lucaskirschner/trabajo-final-cese/memoria/Figures/integracion_entradas.pdf

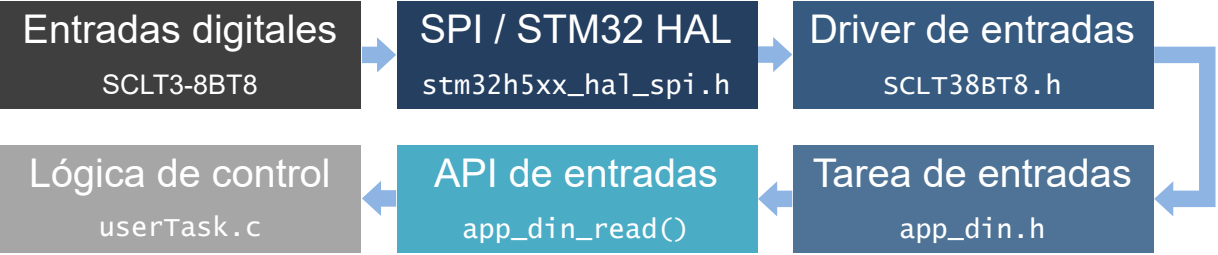
[picture p3: figure]
Entradas digitales; SCLT3-8BT8; SPI / STM32 HAL; stm32h5xx_hal_spi.h; Driver de entradas; SCLT38BT8.h; Tarea de entradas; app_din.h; API de entradas; app_din_read(); Lógica de control; userTask.c
