lucaskirschner/trabajo-final-cese/memoria/Figures/integracion_rf.pdf

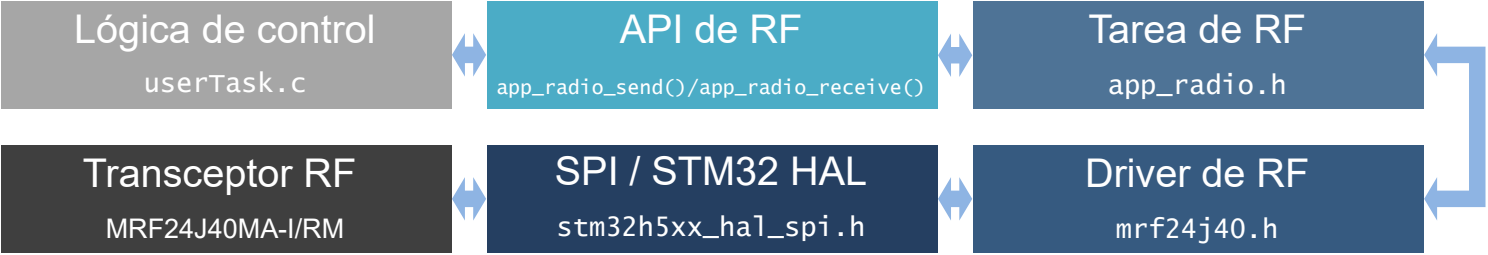
[picture p4: figure]
Transceptor RF; MRF24J40MA-I/RM; SPI / STM32 HAL; stm32h5xx_hal_spi.h; Driver de RF; mrf24j40.h; Lógica de control; userTask.c; API de RF; app_radio_send()/app_radio_receive(); Tarea de RF; app_radio.h
