lucaskirschner/trabajo-final-cese/memoria/Figures/integracion_rs485.pdf

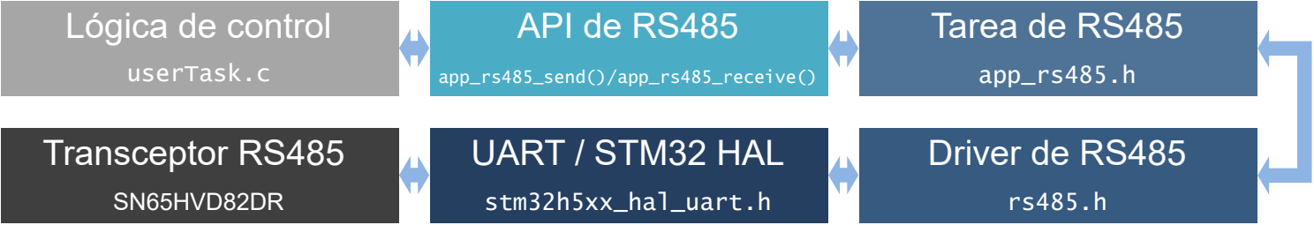
[picture p5: figure]
Transceptor RS485; SN65HVD82DR; UART / STM32 HAL; stm32h5xx_hal_uart.h; Driver de RS485; Lógica de control; userTask.c; API de RS485; app_rs485_send()/app_rs485_receive(); Tarea de RS485; app_rs485.h
