lucaskirschner/trabajo-final-cese/memoria/Figures/integracion_salidas.pdf

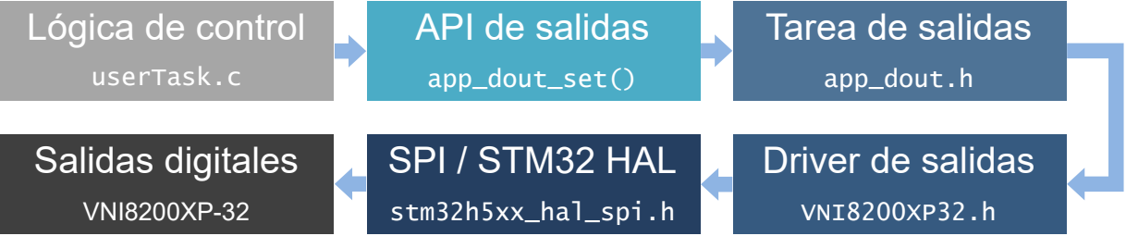
[picture p6: figure]
Salidas digitales; VNI8200XP-32; SPI / STM32 HAL; stm32h5xx_hal_spi.h; Driver de salidas; VNI8200XP32.h; Lógica de control; userTask.c; API de salidas; app_dout_set(); Tarea de salidas; app_dout.h
