lucaskirschner/trabajo-final-cese/memoria/Figures/red_control_distribuida.pdf

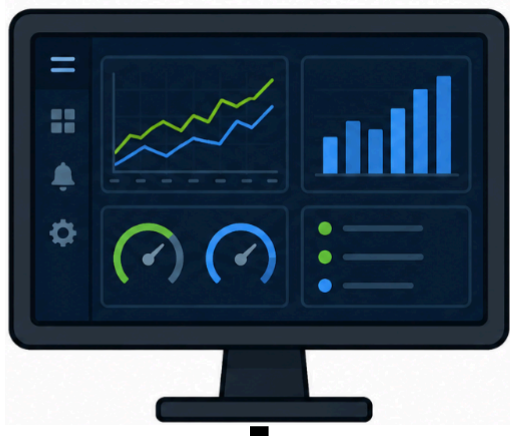
[picture p8: figure]

## SUPERVISIÓN

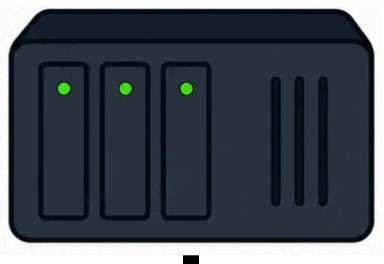
[picture p9: figure]

## CONTROL

## CAMPO

INTERFAZ DE
SUPERVISIÓN

ESTACIÓN
CENTRAL

ESTACIÓN
REMOTA 1

ESTACIÓN
REMOTA 2

SENSOR DE

PROXIMIDAD | CONTACTOR | SENSOR DE
CAUDAL | ELECTROVÁLVULA
