lucaskirschner/trabajo-final-cese/memoria/Releases/TI_Kirschner_Lucas_V4_vs_V5.pdf

# Draftable Comparison Export

This document is an exported comparison with limited functionality, generated by Draftable Desktop. To access full functionality, use Draftable's powerful comparison viewer in any of our products.
Left document: | TI_Kirschner_Lucas_V4.pdf
Right document: | TI_Kirschner_Lucas_V5.pdf

## What is this document?

This is a comparison of two documents. The two documents are interleaved such that the left document is displayed on even pages and the right document is displayed on odd pages.

## Is there a specific way I should view this file?

This document is intended to be viewed in Two Page Continuous mode (or sometimes called 'Two Page Scrolling'). It should open in this mode by default when using Adobe Acrobat and most popular PDF readers.

If the document opens in a different view, you can often change this in the settings. In Adobe Acrobat, go to View > Page Display > Two Page Scrolling.

## Why are there blank pages?

Blank pages are inserted to keep both documents as aligned as much as possible.
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
