lucaskirschner/trabajo-final-cese/hardware/dev/Rev/MEC-V1.0-Sch RevA.pdf

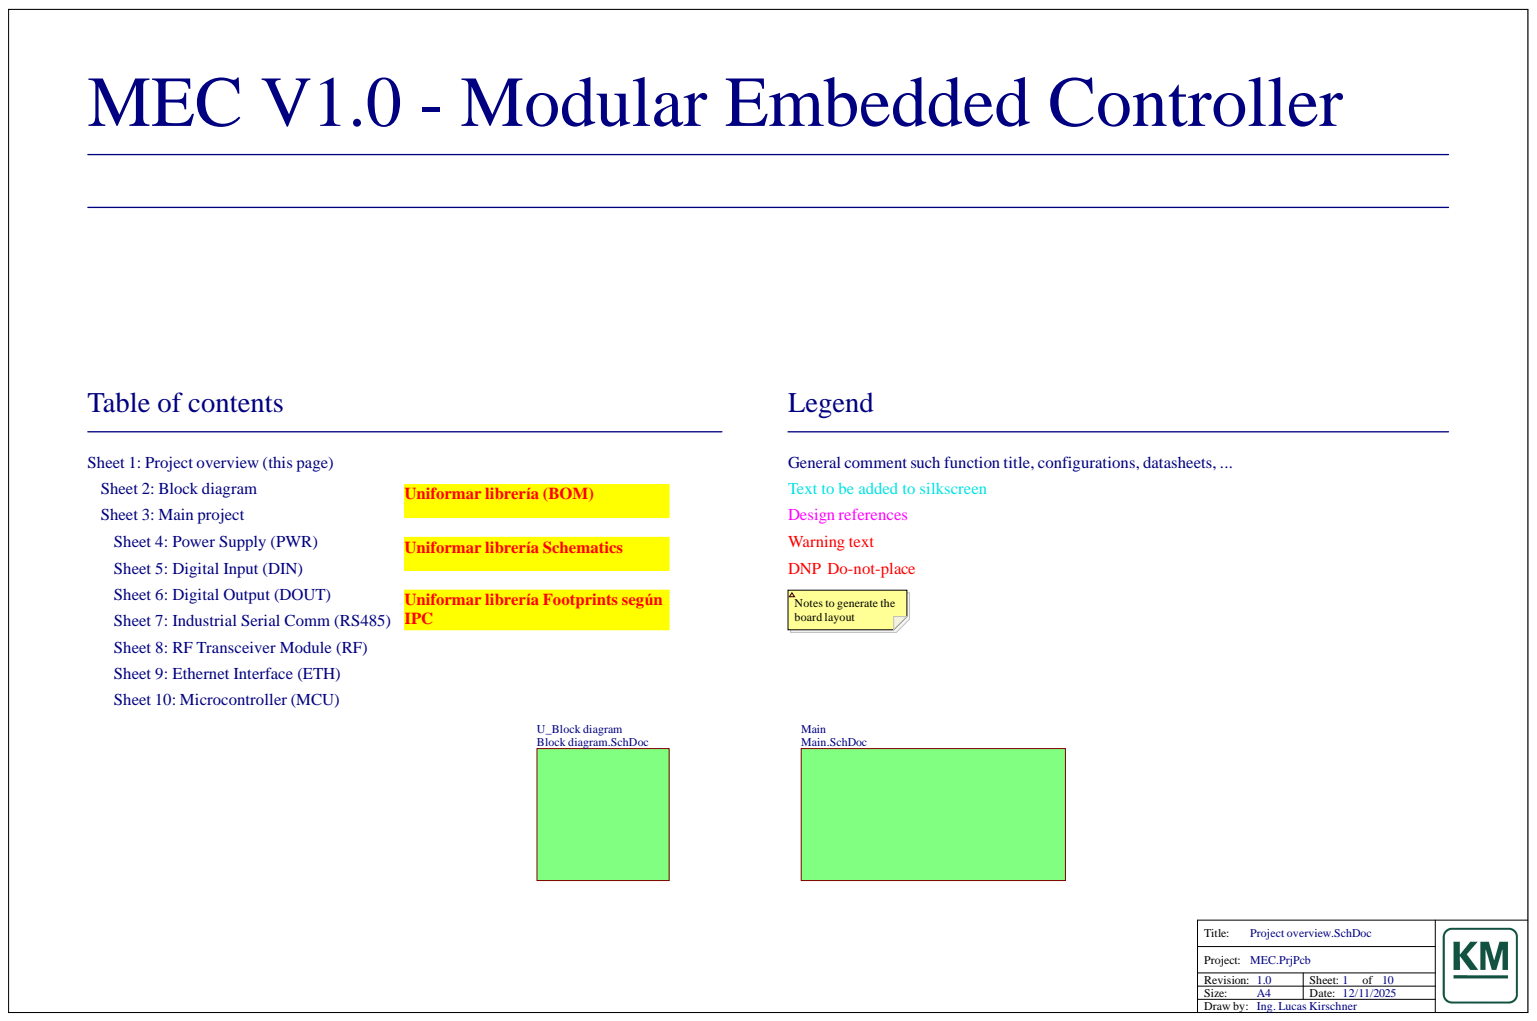
[picture p63: page 1]

MEC V1.0 - Modular Embedded Controller

Sheet 1: Project overview (this page)
Sheet 2: Block diagram
Sheet 3: Main project
Sheet 4: Power Supply (PWR)
Sheet 5: Digital Input (DIN)
Sheet 6: Digital Output (DOUT)
Sheet 7: Industrial Serial Comm (RS485)
Sheet 8: RF Transceiver Module (RF)
Sheet 9: Ethernet Interface (ETH)
Sheet 10: Microcontroller (MCU)

General commentsuch function title, configurations, datasheets, ...
Text to be added to silkscreen
Design references
Warning text
DNP Do-not-place

Uniformar librería Footprints según
IPC

Notes to generate the
board layout

Revision: 1.0 | Sheet: 1 of 10
Size: A4 | Date:


Reservado diagrama de bloques

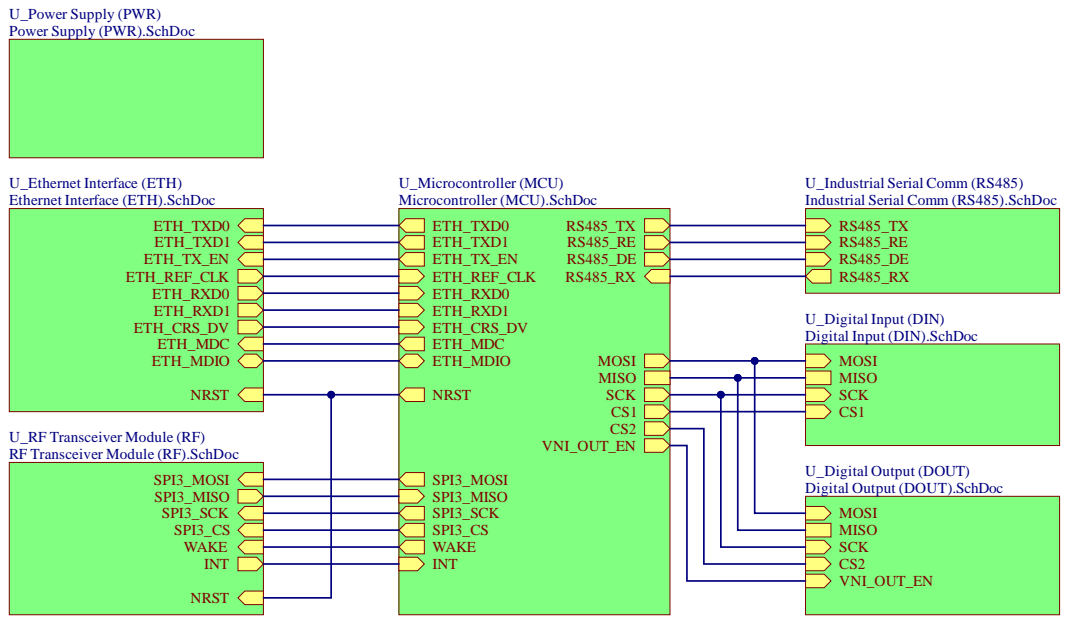
[picture p64: page 3]

U_Power Supply (PWR)
Power Supply (PWR).SchDoc

U_Ethernet Interface (ETH)
Ethernet Interface (ETH).SchDoc

U_RF Transceiver Module (RF)
RF Transceiver Module (RF).SchDoc

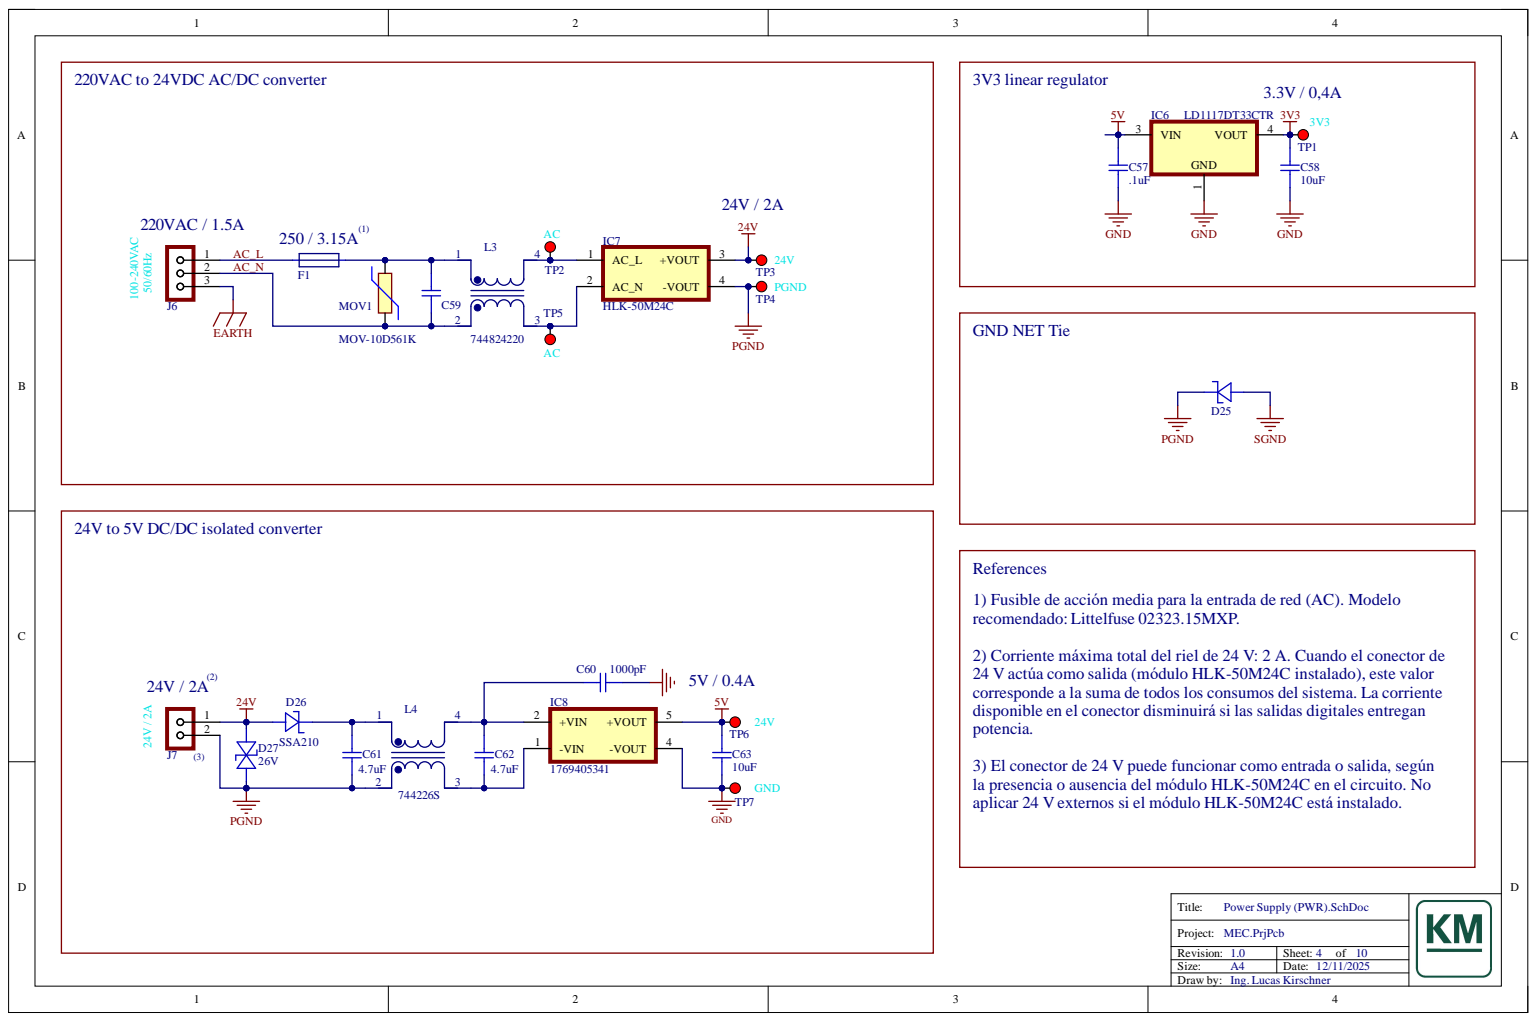
[picture p65: page 4]

220VAC to 24VDC AC/DC converter

24V to 5V DC/DC isolated converter

1) Fusible de acción media para la entrada de red (AC). Modelo
recomendado: Littelfuse 02323.15MXP.

2) Corriente máxima total del riel de 24 V: 2 A. Cuando el conector de
24 V actúa como salida (módulo HLK-50M24C instalado), este valor
corresponde a la suma de todos los consumos del sistema. La corriente
disponible en el conector disminuirá si las salidas digitales entregan
potencia.

3) El conector de 24 V puede funcionar como entrada o salida, según
la presencia o ausencia del módulo HLK-50M24C en el circuito. No
aplicar 24 V externos si el módulo HLK-50M24C está instalado.

Power Supply (PWR).SchDoc

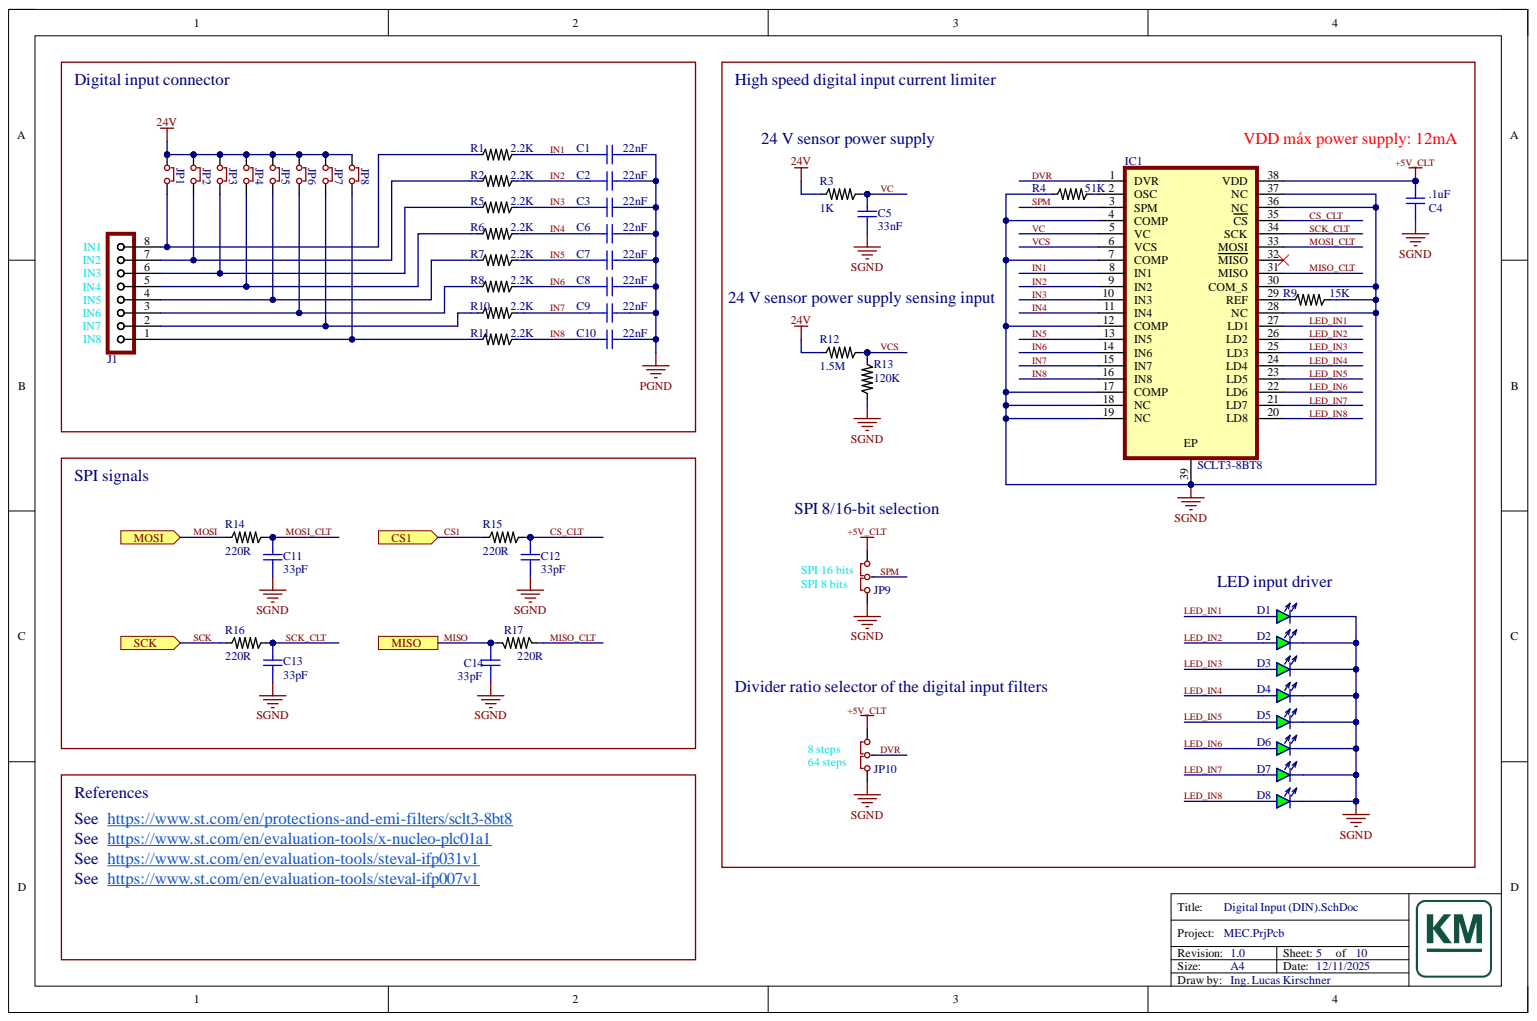
[picture p66: page 5]

3 5 3 4 3 3 3 2 | C S_C LT S CK_C LT MOS I_C LT M I SO_C LT

V sensor power supply sensing

Rev i s i o n : 1 . 0 | Sheet : o f 1 0
Size : A | Dat e : / /

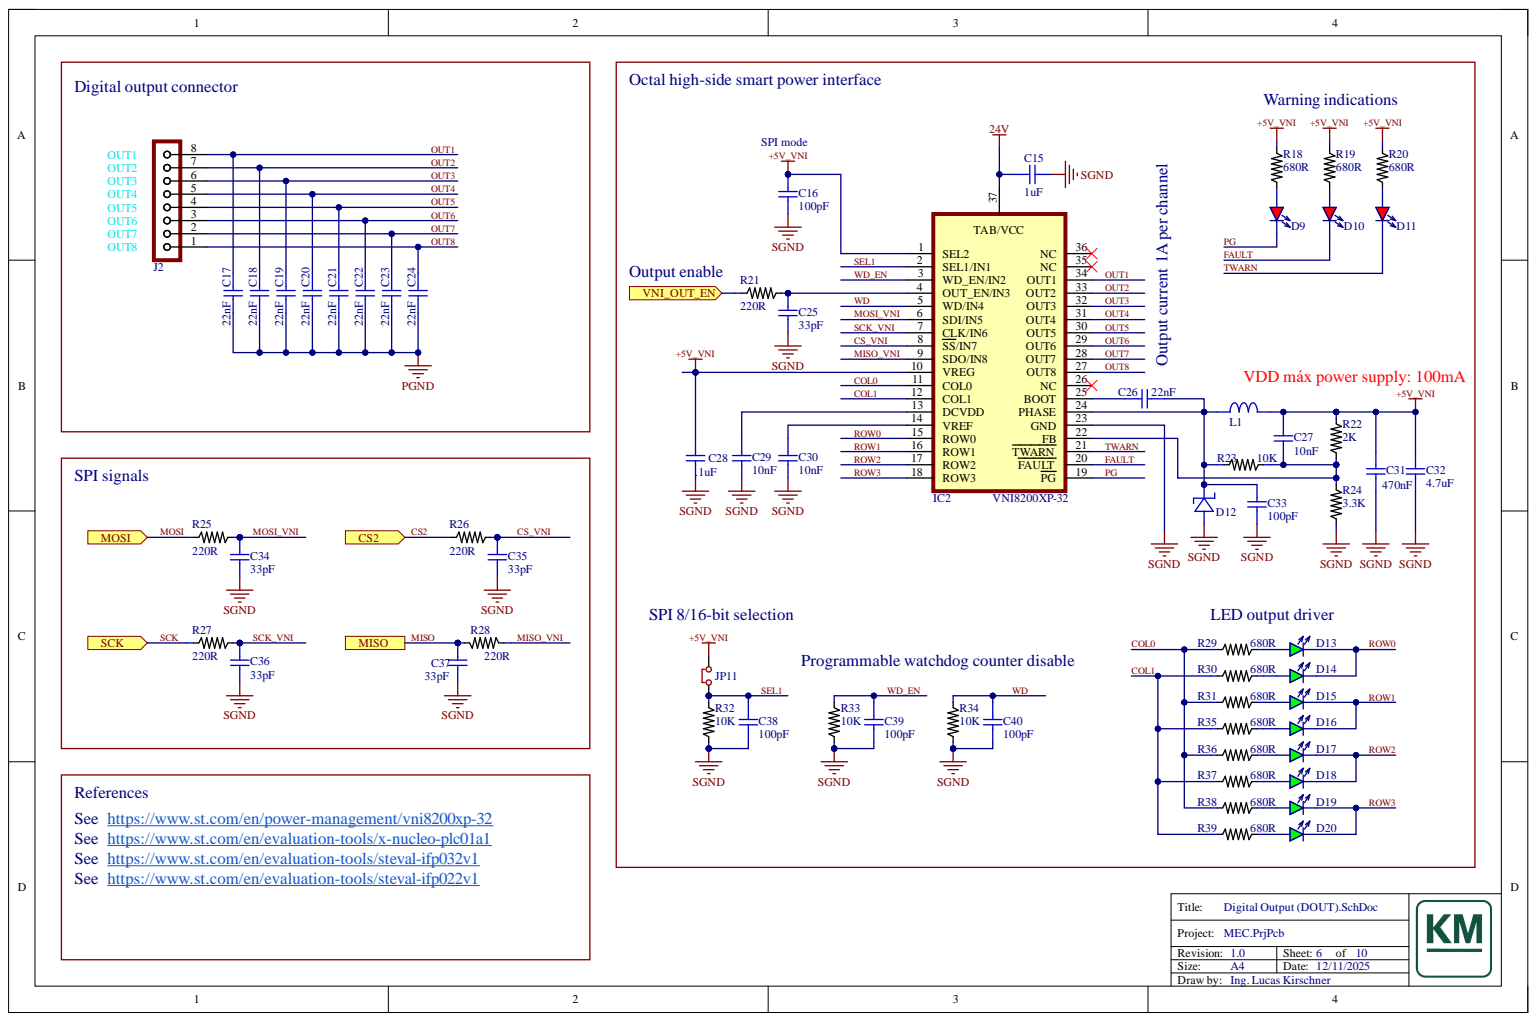
[picture p67: page 6]

Warning indications +5V_VNI +5V_VNI +5V_VNI

Output current 1A per channel

VDD máx power supply: 100mA

Programmable watchdog counter disable

References
See https://www.st.com/en/power-management/vni8200xp-32
See https://www.st.com/en/evaluation-tools/x-nucleo-plc01a1
See https://www.st.com/en/evaluation-tools/steval-ifp032v1
See https://www.st.com/en/evaluation-tools/steval-ifp022v1

Digital Output (DOUT).SchDoc

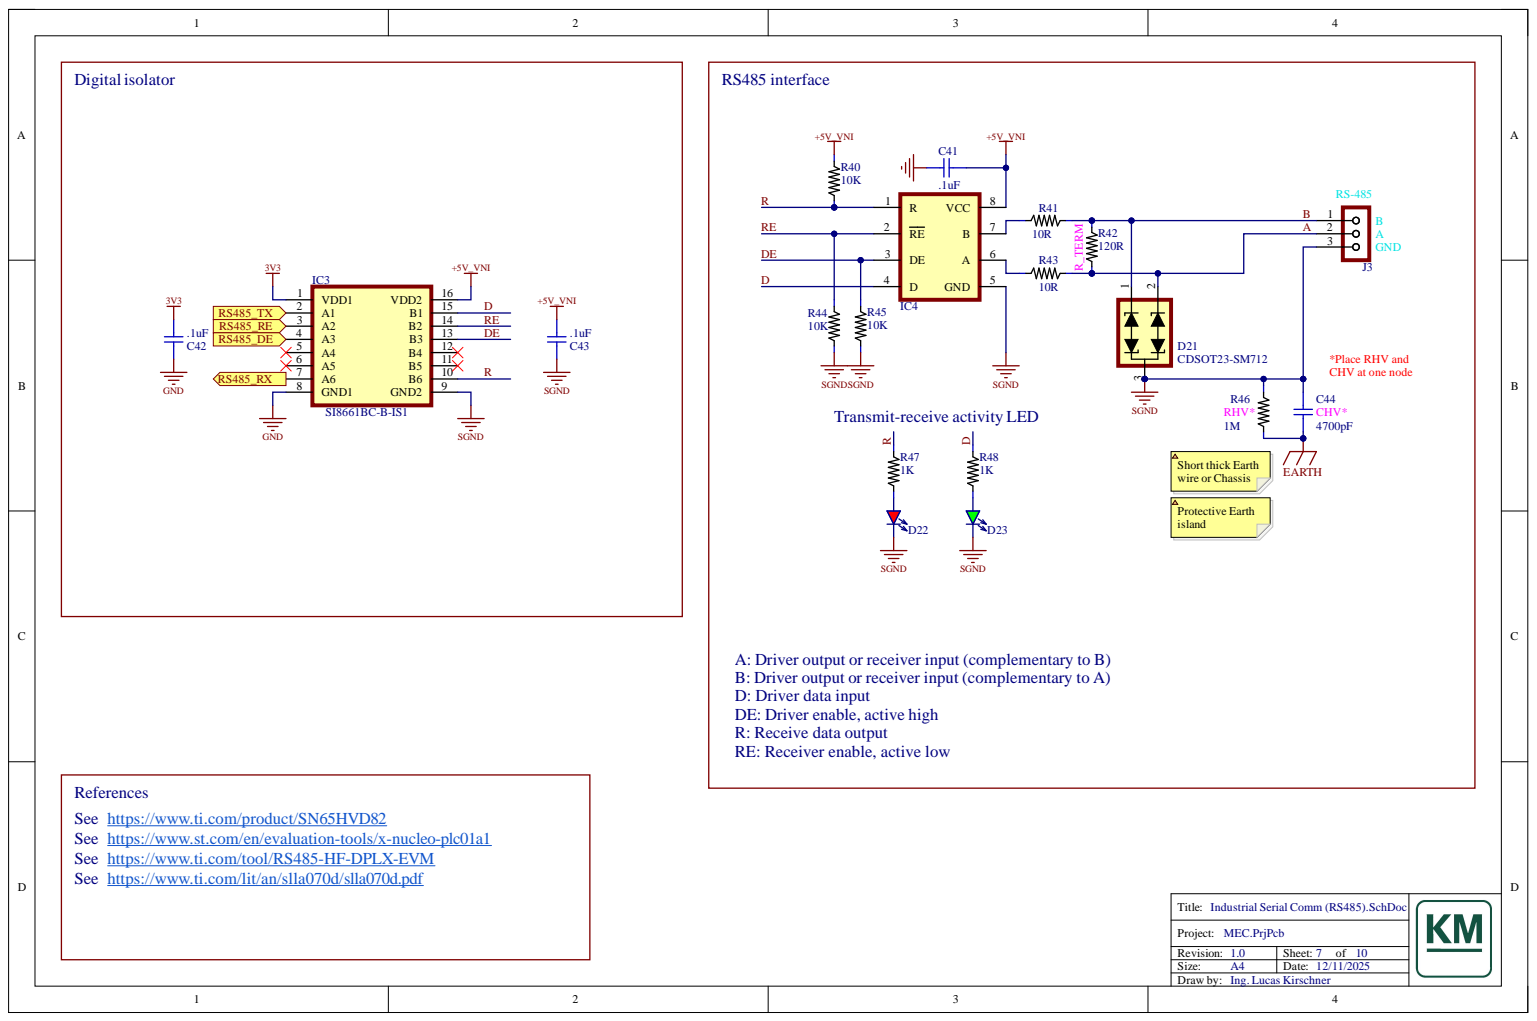
[picture p68: page 7]

Driver output or receiver

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

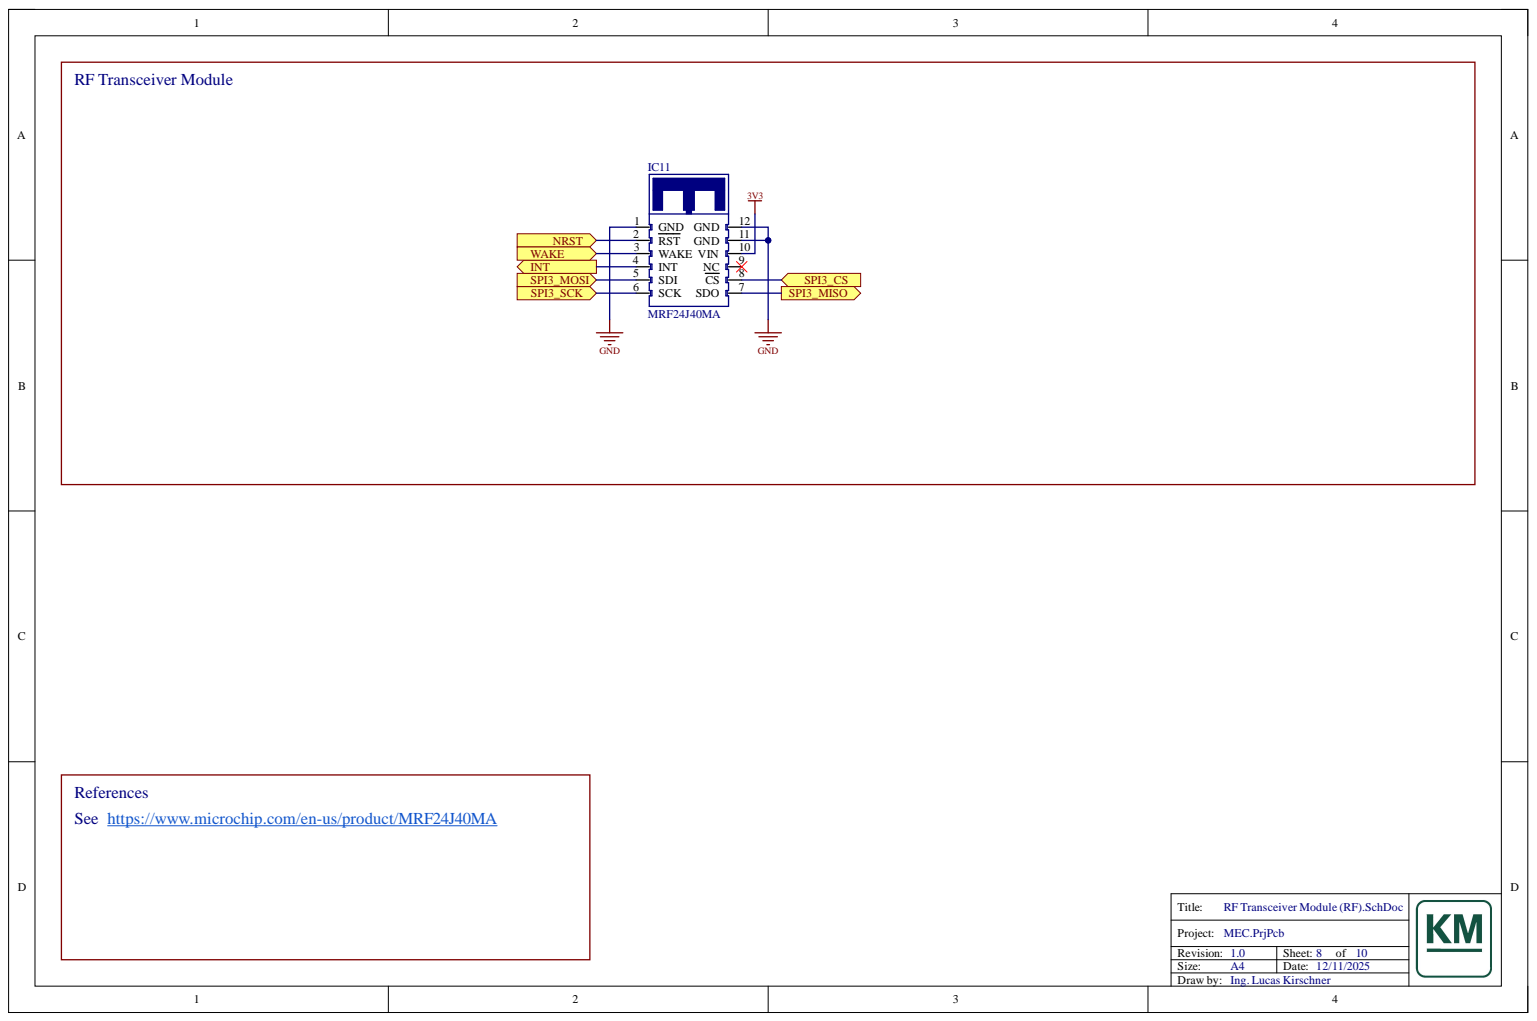
[picture p69: page 8]

References
See https://www.microchip.com/en-us/product/MRF24J40MA

RF Transceiver Module (RF).SchDoc

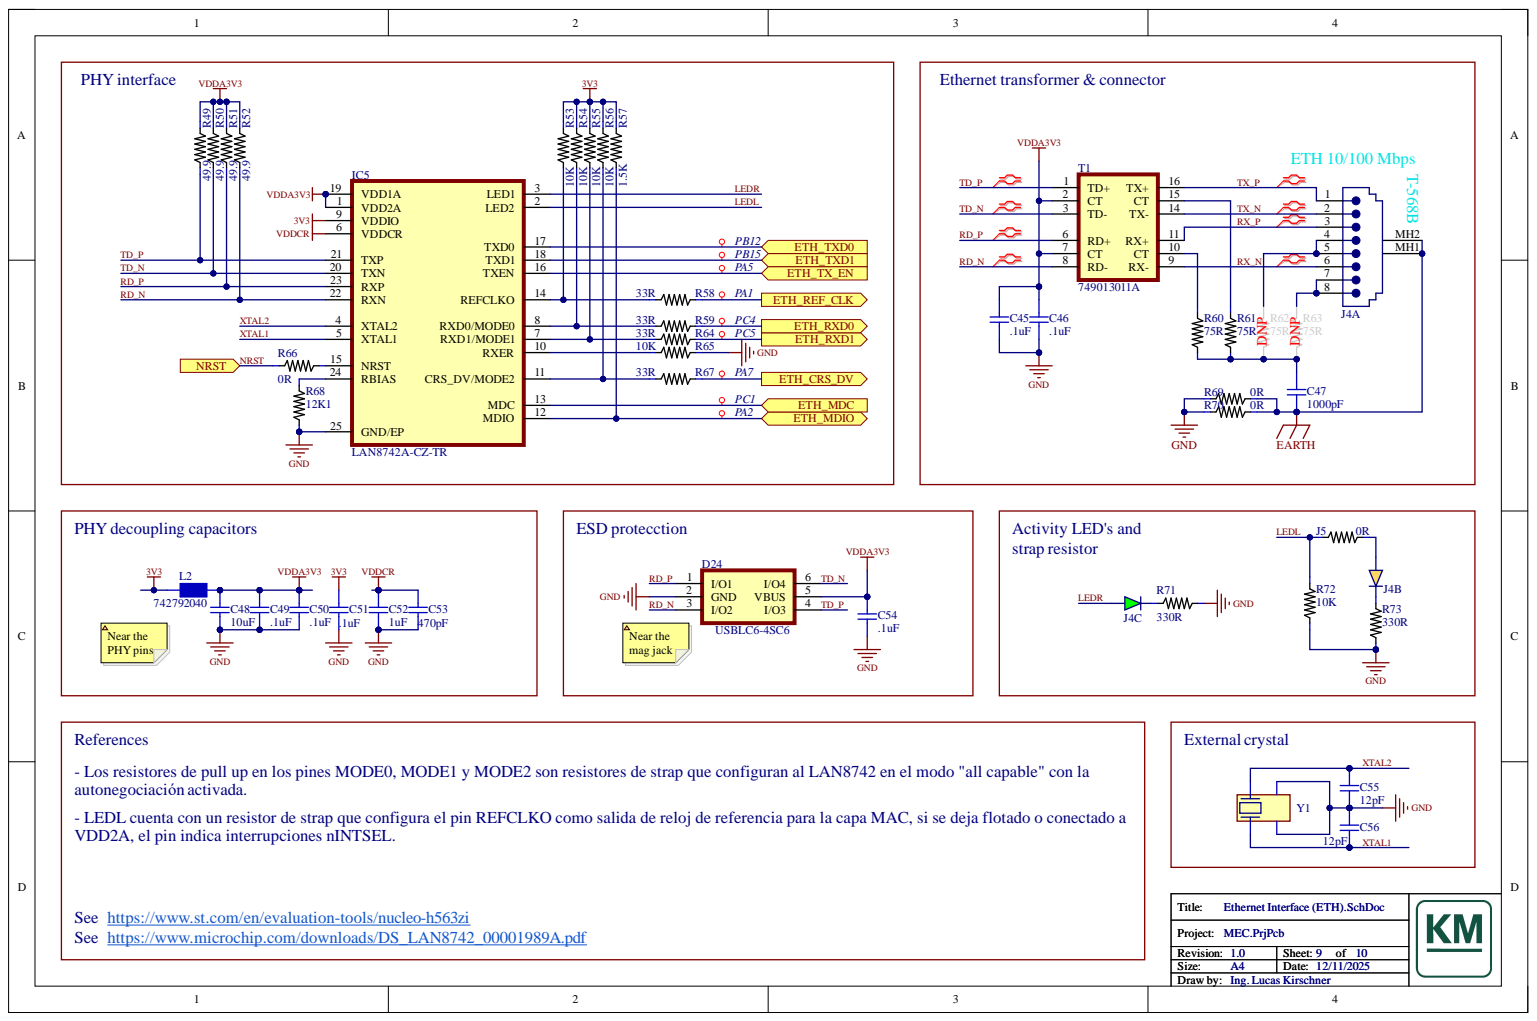
[picture p70: page 9]

- Los resistores de pull up en los pines MODE0, MODE1 y MODE2 son resistores de strap que configuran al LAN8742 en el modo "all capable" con la
autonegociación activada.
- LEDL cuenta con un resistor de strap que configura el pin REFCLKO como salida de reloj de referencia para la capa MAC, si se deja flotado o conectado a
VDD2A, el pin indica interrupciones nINTSEL.

See https://www.st.com/en/evaluation-tools/nucleo-h563zi
See https://www.microchip.com/downloads/DS_LAN8742_00001989A.pdf (https://ww1.microchip.com/downloads/aemDocuments/documents/OTH/ProductDocuments/DataSheets/DS_LAN8742_00001989A.pdf)

Ethernet Interface (ETH).SchDoc

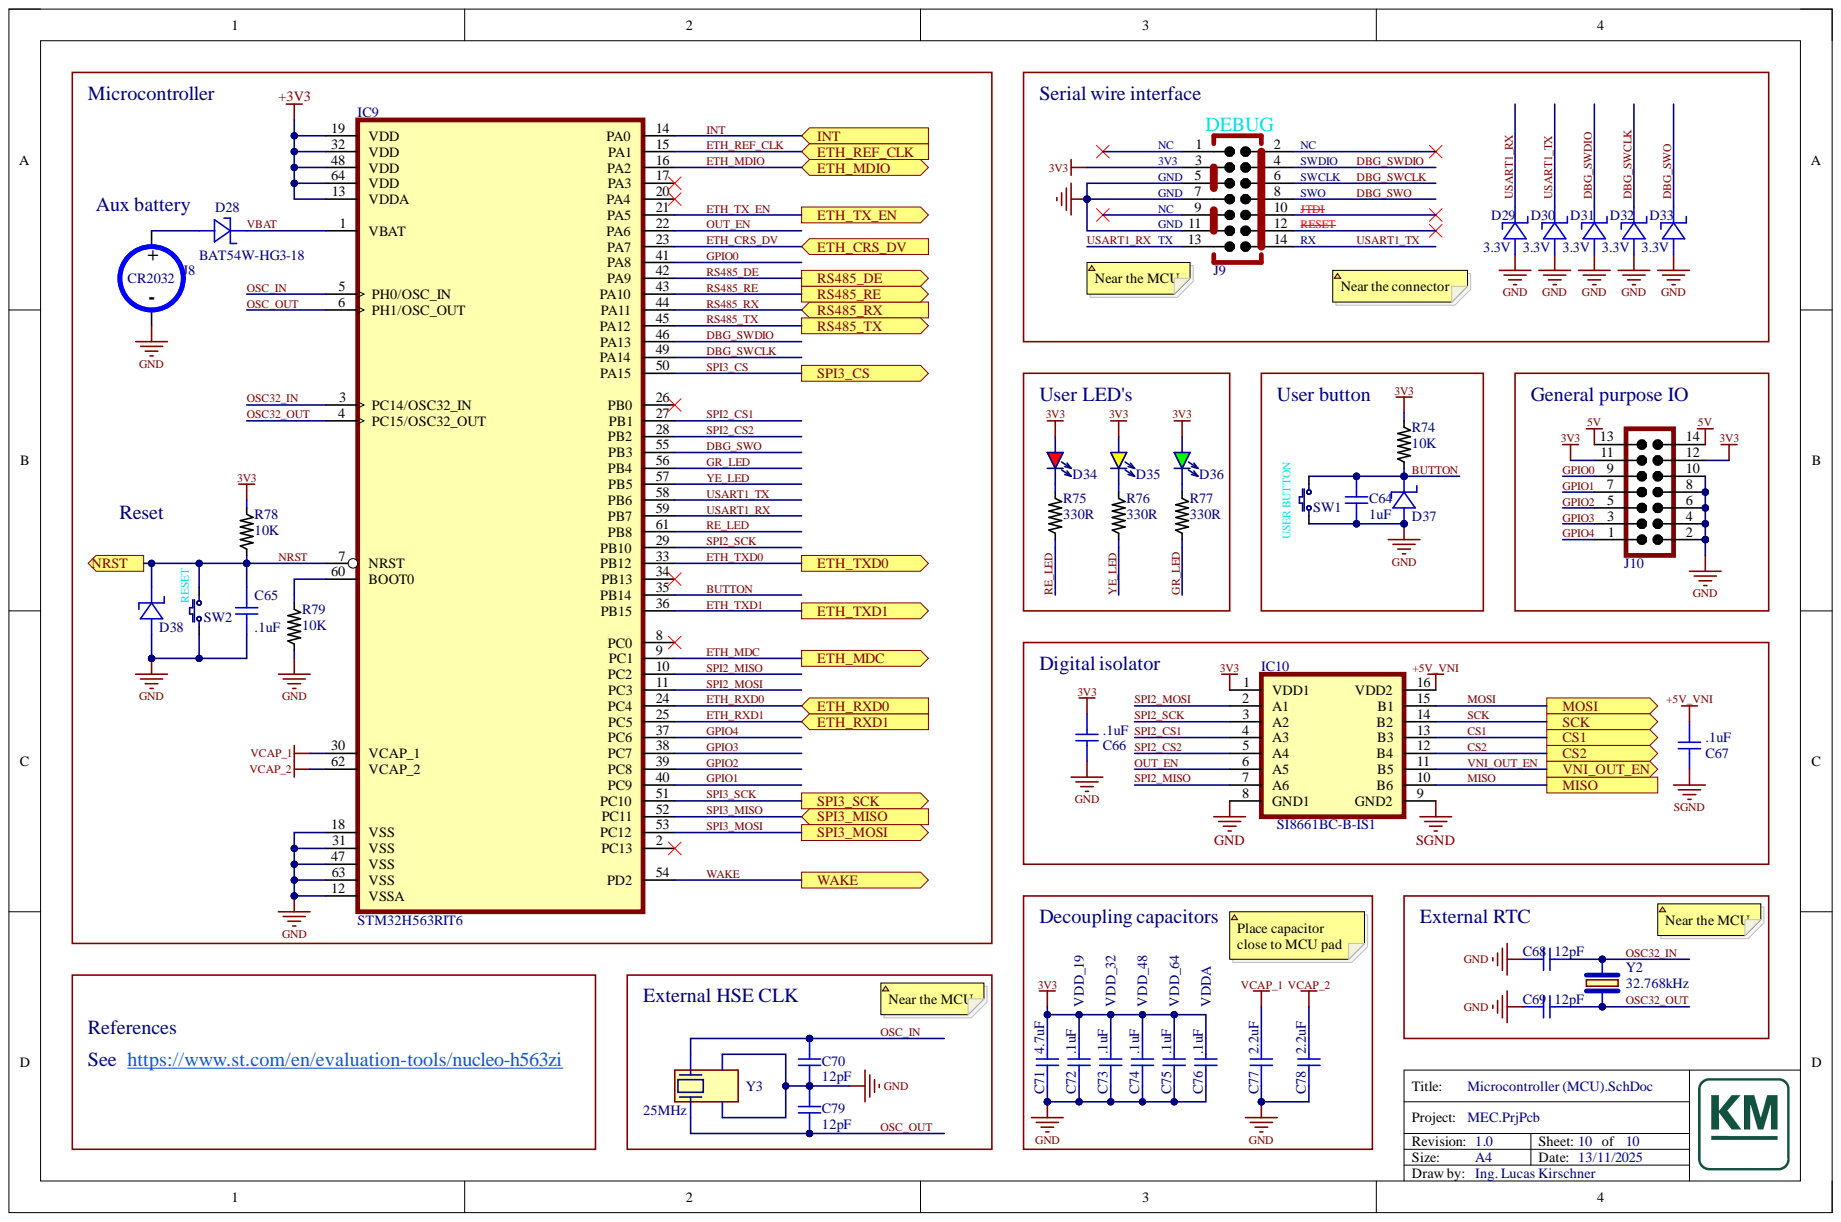
[picture p71: page 10]
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
