lucaskirschner/trabajo-final-cese/hardware/dev/Rev/MEC-V1.0-Sch RevB.pdf

MEC V1.0 - Modular Embedded Controller

Sheet 1: Project overview (this page)
Sheet 2: Block diagram
Sheet 3: Main project
Sheet 4: Power Supply (PWR)
Sheet 5: Digital Input (DIN)
Sheet 6: Digital Output (DOUT)
Sheet 7: Industrial Serial Comm (RS485)
Sheet 8: RF Transceiver Module (RF)
Sheet 9: Ethernet Interface (ETH)
Sheet 10: Microcontroller (MCU)

General commentsuch function title, configurations, datasheets, ...
Text to be added to silkscreen
Design references
Warning text
DNP Do-not-place

Uniformar librería Footprints según
IPC

Notes to generate the
board layout

Revision: 1.0 | Sheet: 1 of 10
Size: A4 | Date:


Reservado diagrama de bloques


U_Power Supply (PWR)
Power Supply (PWR).SchDoc

U_Ethernet Interface (ETH)
Ethernet Interface (ETH).SchDoc

U_RF Transceiver Module (RF)
RF Transceiver Module (RF).SchDoc

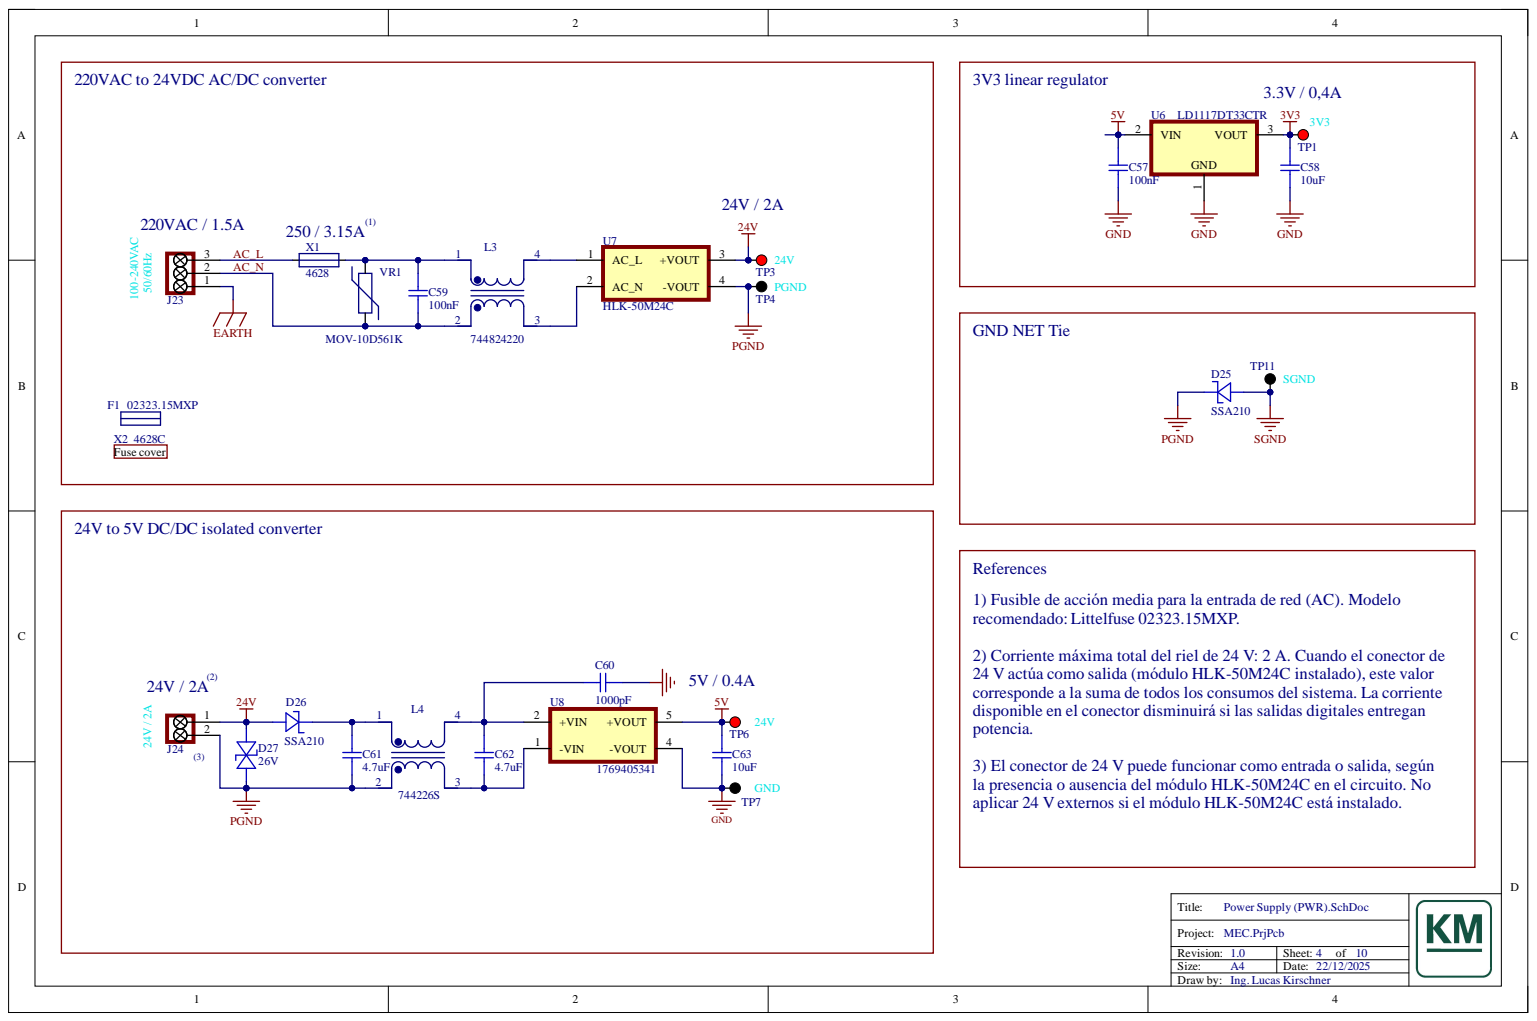
[picture p72: page 4]

220VAC to 24VDC AC/DC converter

24V to 5V DC/DC isolated converter

1) Fusible de acción media para la entrada de red (AC). Modelo
recomendado: Littelfuse 02323.15MXP.

2) Corriente máxima total del riel de 24 V: 2 A. Cuando el conector de
24 V actúa como salida (módulo HLK-50M24C instalado), este valor
corresponde a la suma de todos los consumos del sistema. La corriente
disponible en el conector disminuirá si las salidas digitales entregan
potencia.

3) El conector de 24 V puede funcionar como entrada o salida, según
la presencia o ausencia del módulo HLK-50M24C en el circuito. No
aplicar 24 V externos si el módulo HLK-50M24C está instalado.

Power Supply (PWR).SchDoc

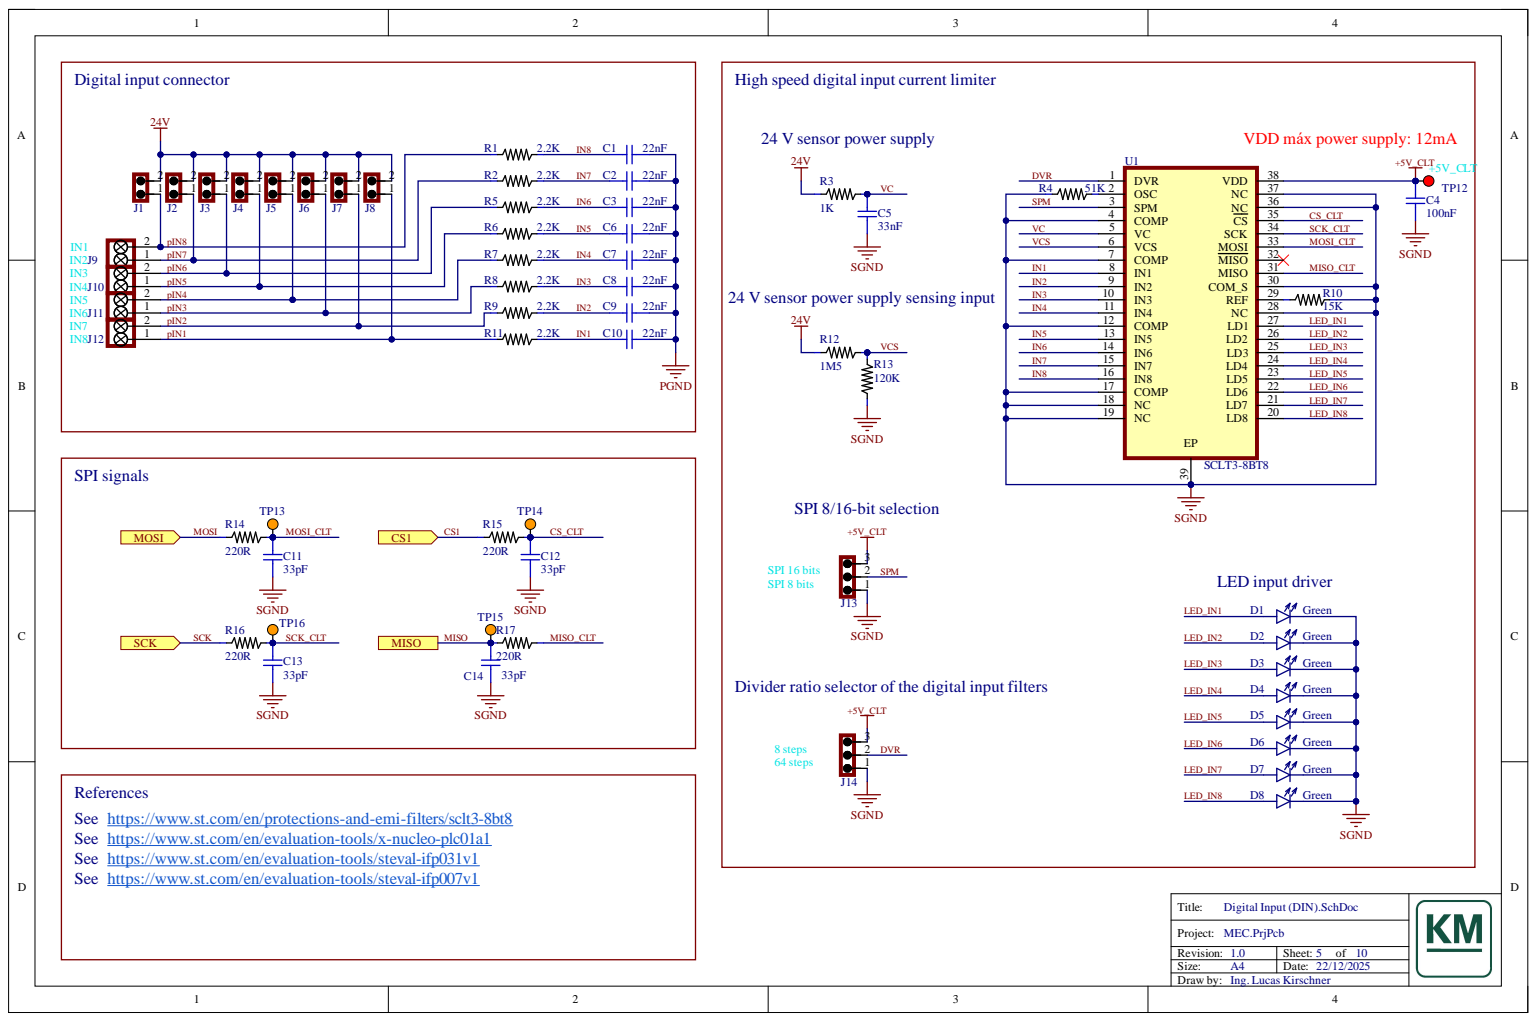
[picture p73: page 5]

pIN7 | R7

V sensor power supply sensing

Rev i s i o n : 1 . 0 | Sheet : o f 1 0
Size : A | Dat e /

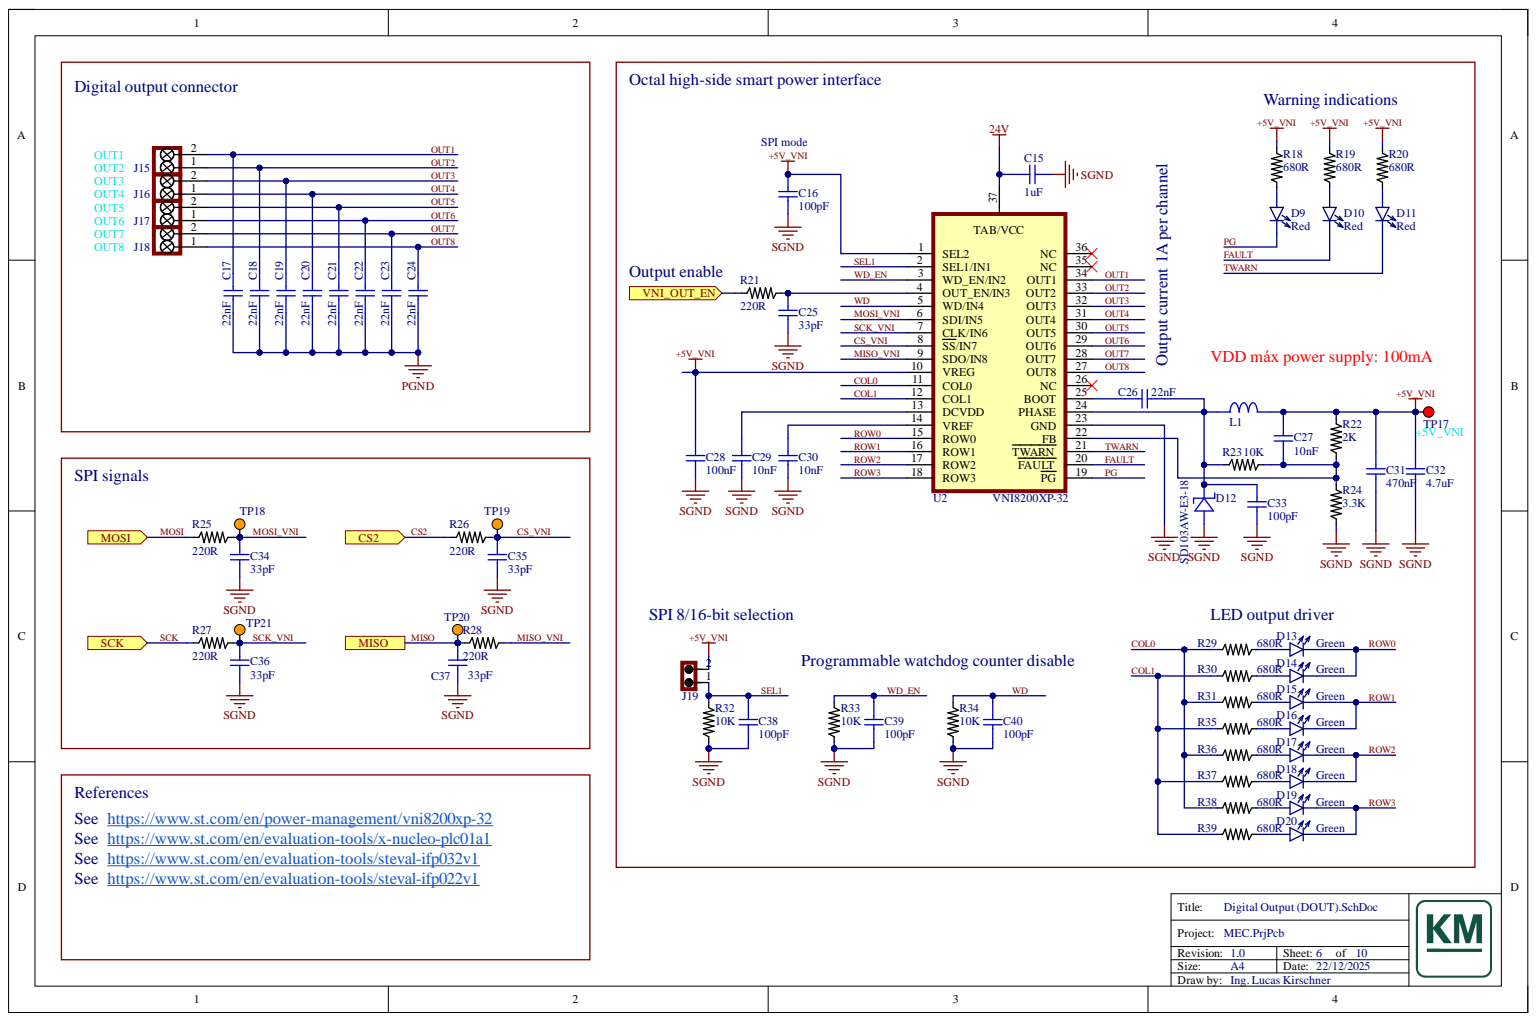
[picture p74: page 6]

Octal high-side smart power

Output current 1A per channel

12 | OUT 3

OUT 4

12 | | | OUT 5

OUT 6

12 | | | | | OUT 7

ion | | 2 1 | FAULT TWARN

SPI signal s SG SG | TP1 8 TP1 C3 4 N D SG TP2 0 TP2 1 C3 6 N D N D | 9 C3 5 N D

/en/power-management/vni
/en/evaluat
.com

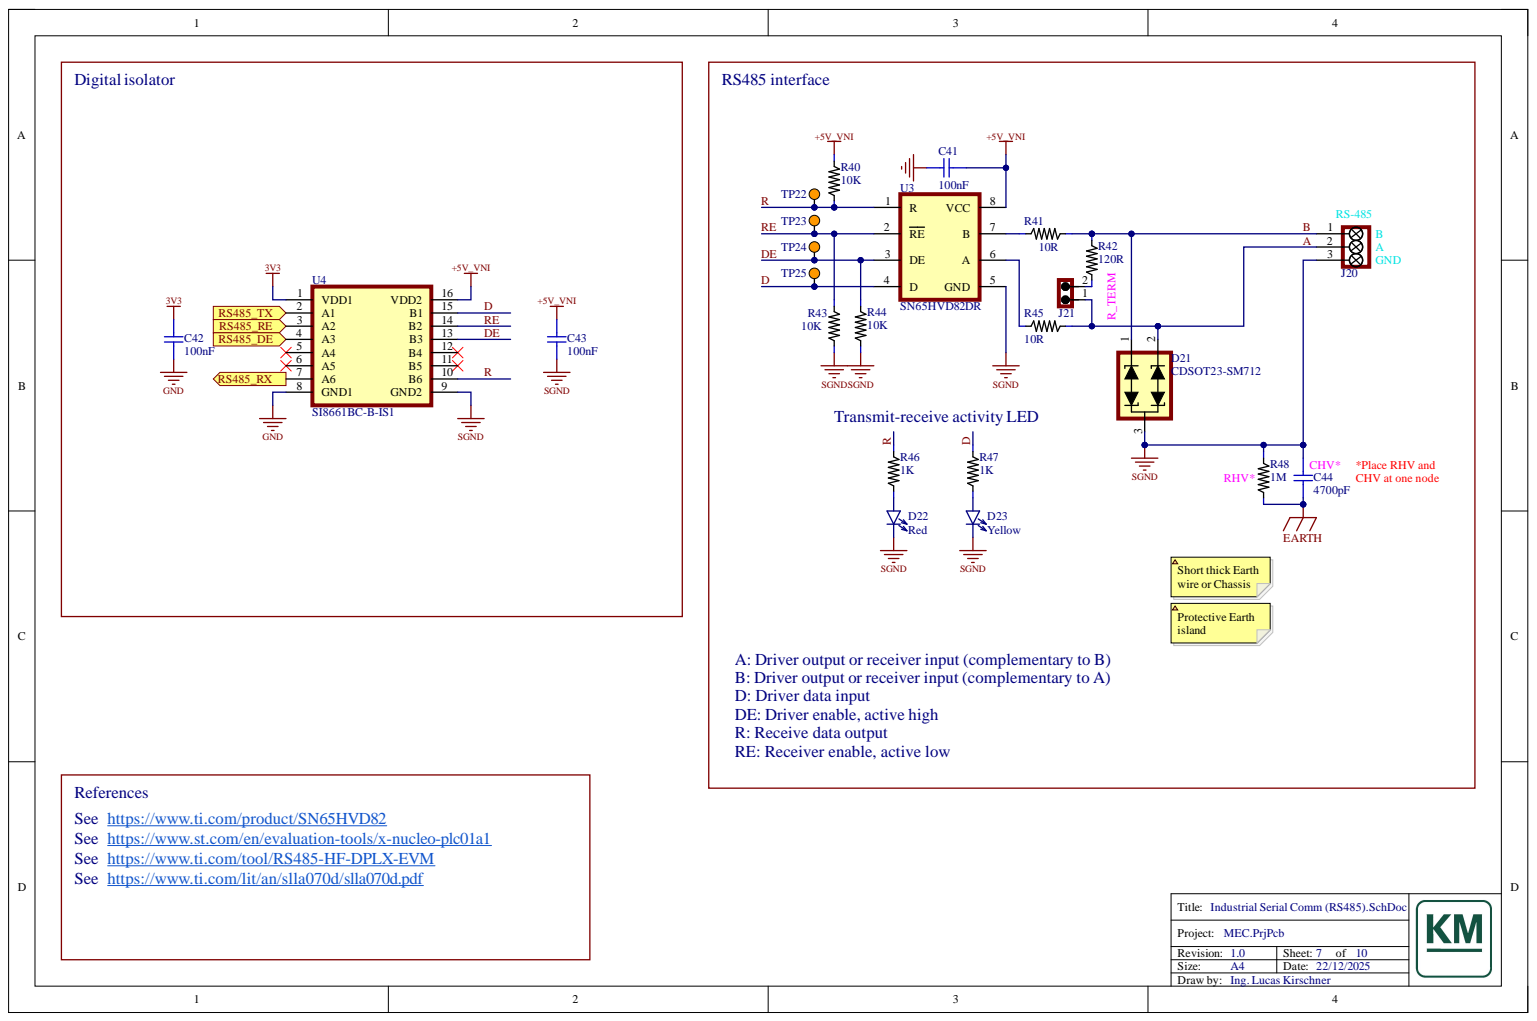
[picture p75: page 7]

Driver output or receiver

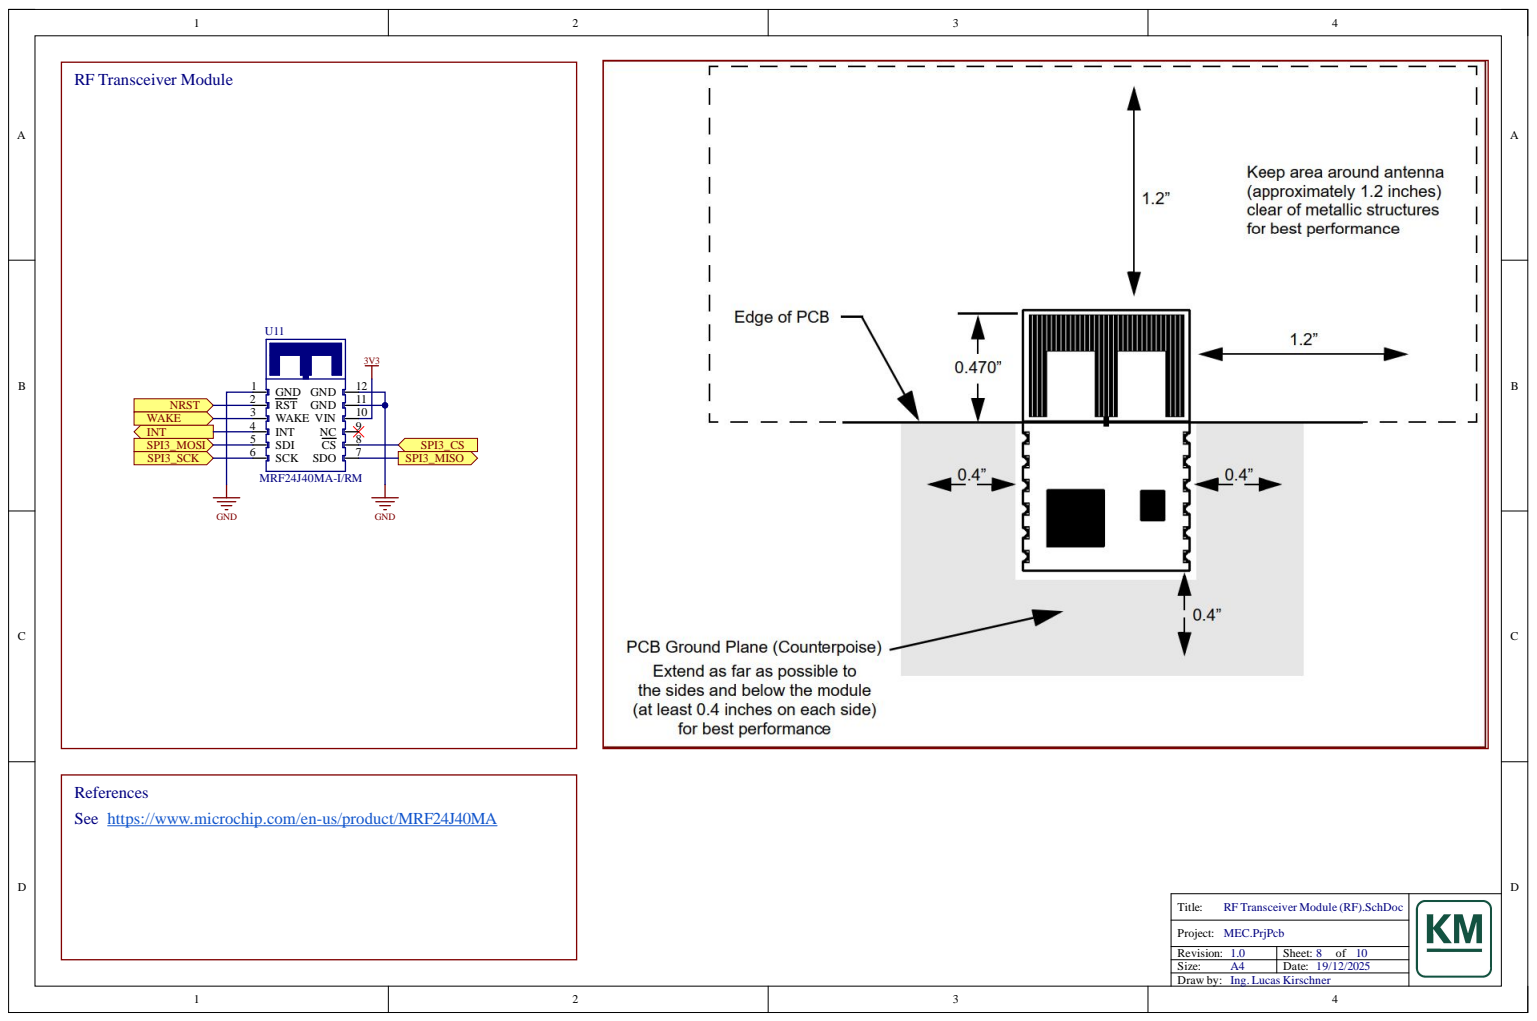
[picture p76: page 8]

References
See https://www.microchip.com/en-us/product/MRF24J40MA

RF Transceiver Module (RF).SchDoc

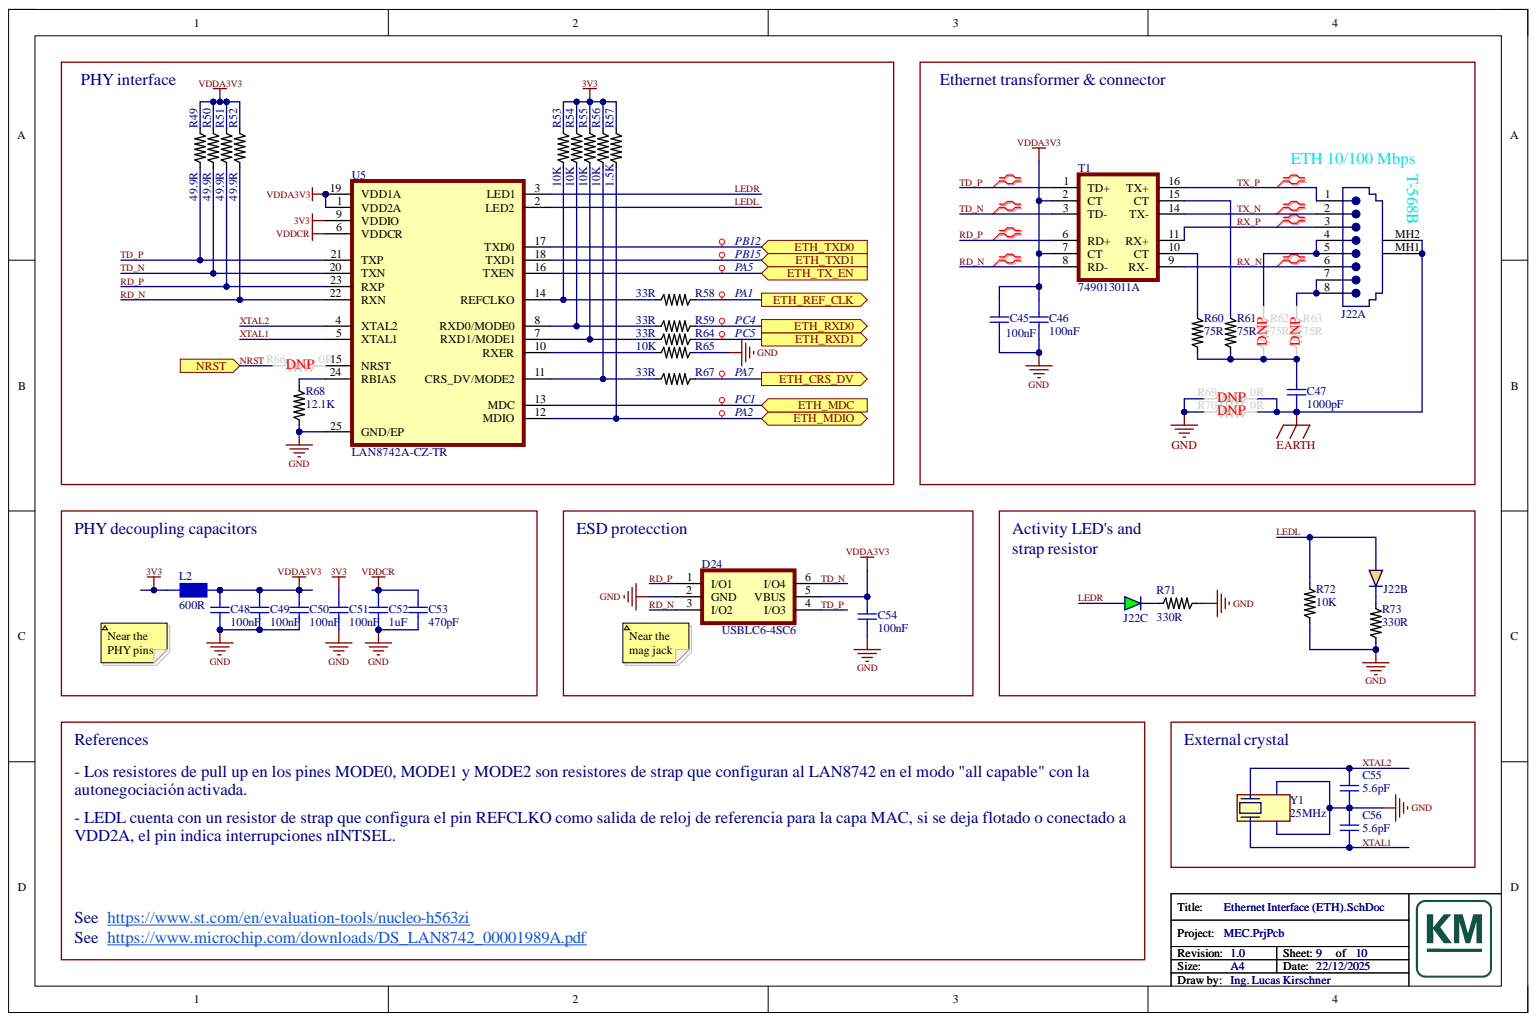
[picture p77: page 9]

- Los resistores de pull up en los pines MODE0, MODE1 y MODE2 son resistores de strap que configuran al LAN8742 en el modo "all capable" con la
autonegociación activada.
- LEDL cuenta con un resistor de strap que configura el pin REFCLKO como salida de reloj de referencia para la capa MAC, si se deja flotado o conectado a
VDD2A, el pin indica interrupciones nINTSEL.

C55
5.6pF

See https://www.st.com/en/evaluation-tools/nucleo-h563zi
See https://www.microchip.com/downloads/DS_LAN8742_00001989A.pdf (https://ww1.microchip.com/downloads/aemDocuments/documents/OTH/ProductDocuments/DataSheets/DS_LAN8742_00001989A.pdf)

Ethernet Interface (ETH).SchDoc

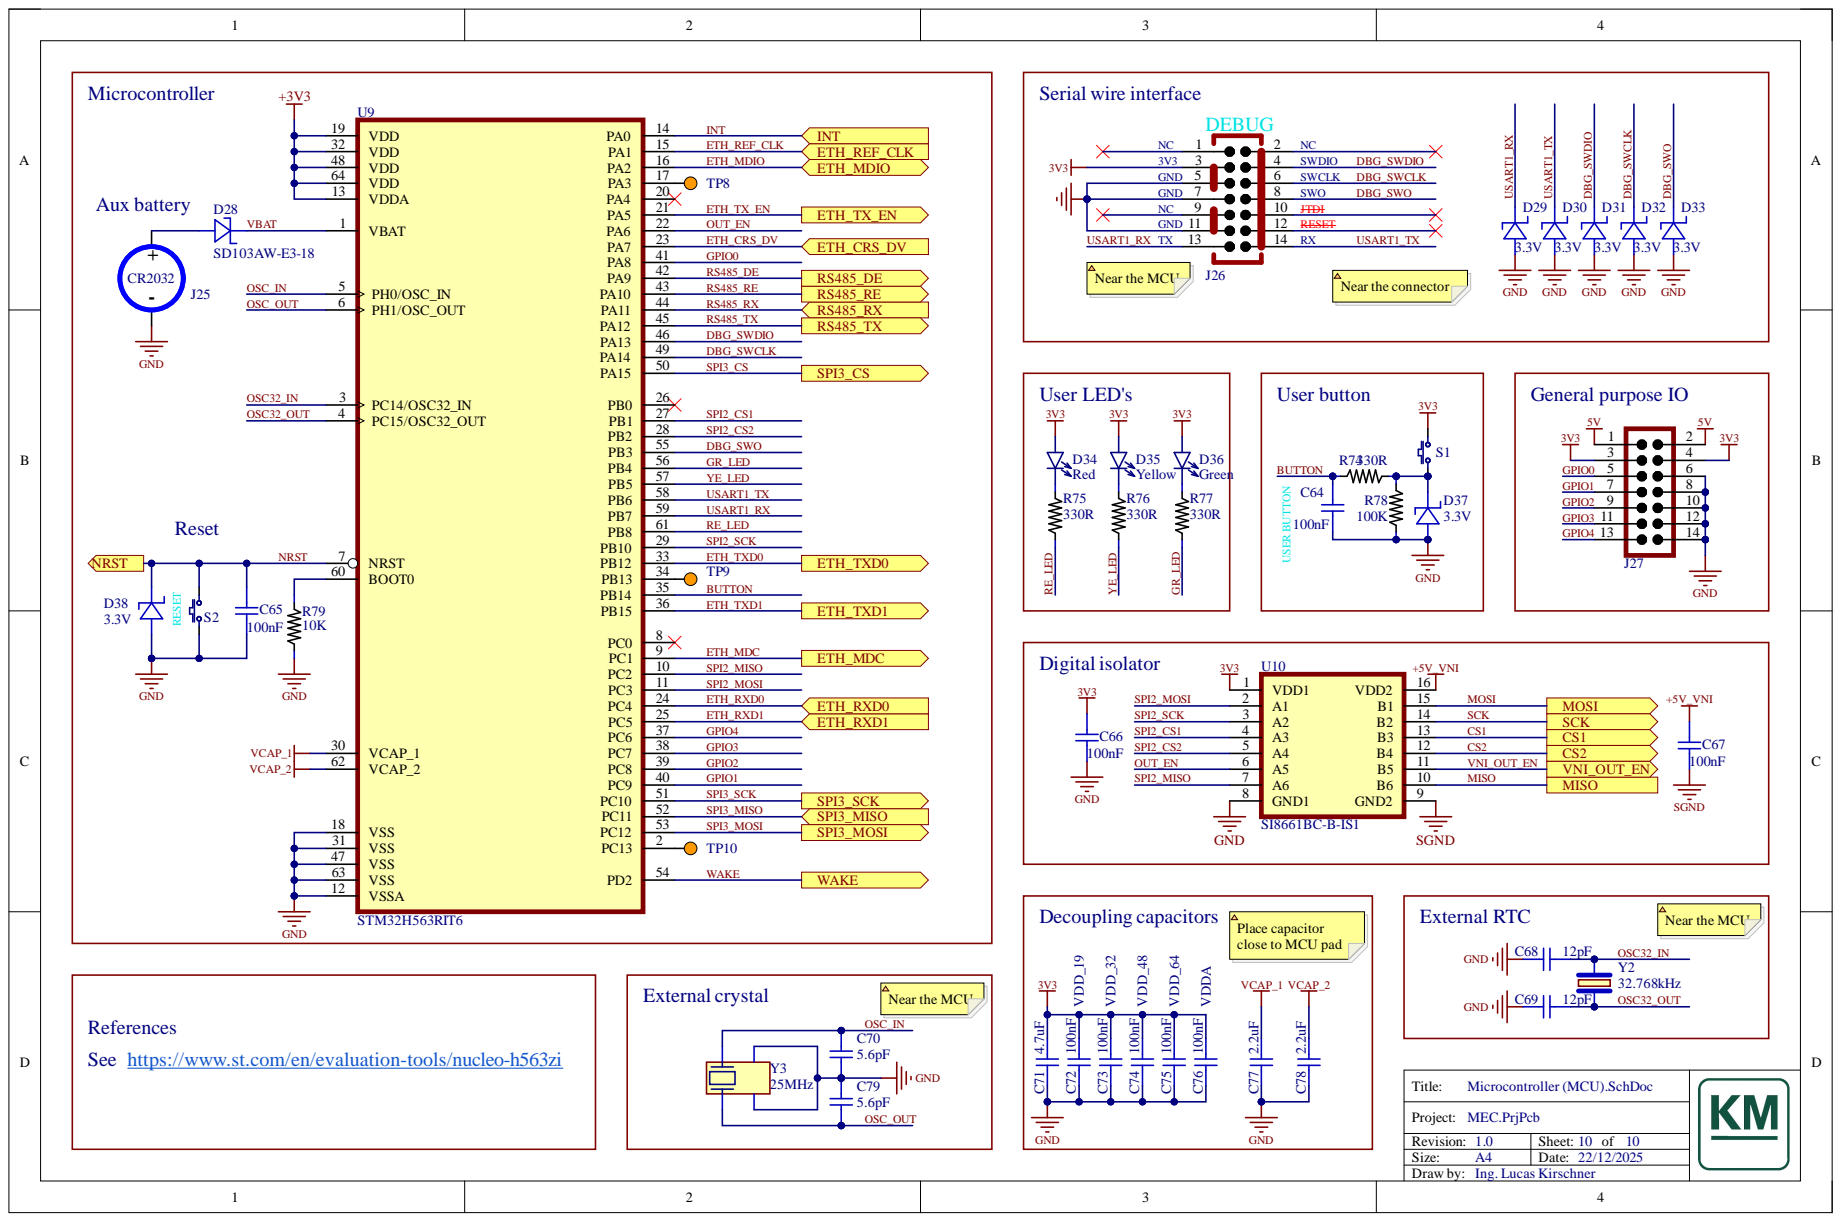
[picture p78: page 10]

C7 0
5.6 p | F
