lucaskirschner/trabajo-final-cese/hardware/doc/Manuales y hojas de datos/STEVAL-IFP032V1 Schematics.pdf

# STEVAL-IFP032V1 Schematic diagram

# Figure 1: STEVAL-IFP032V1 power section

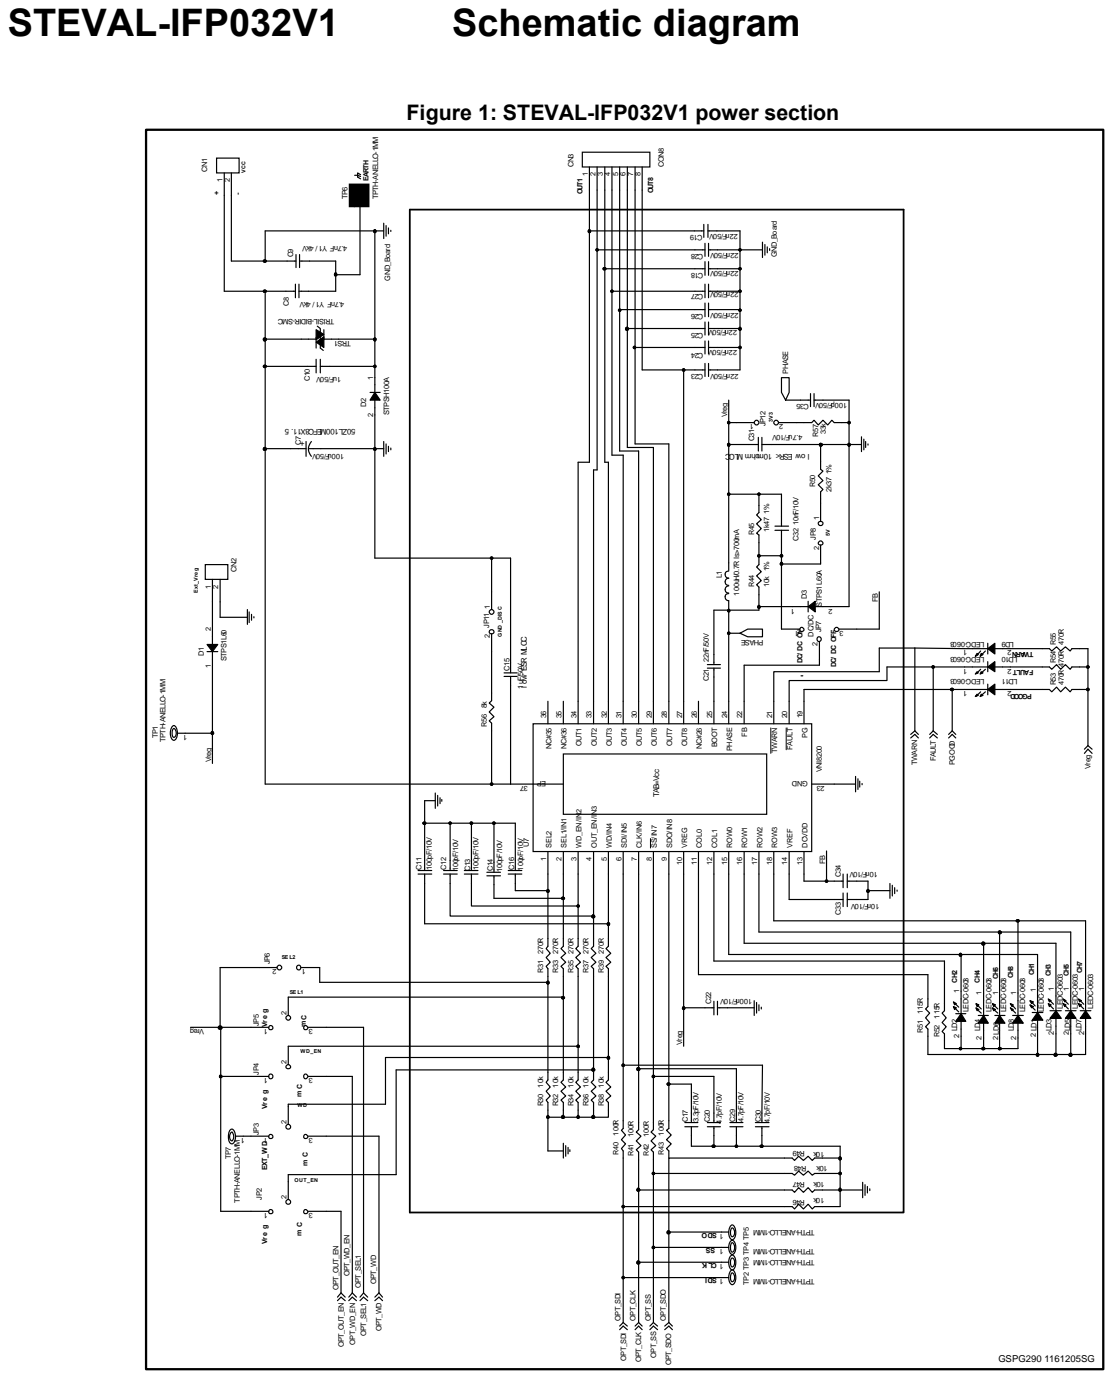
[picture p79: page 1]

# Figure 2: STEVAL-IFP032V1 interface section

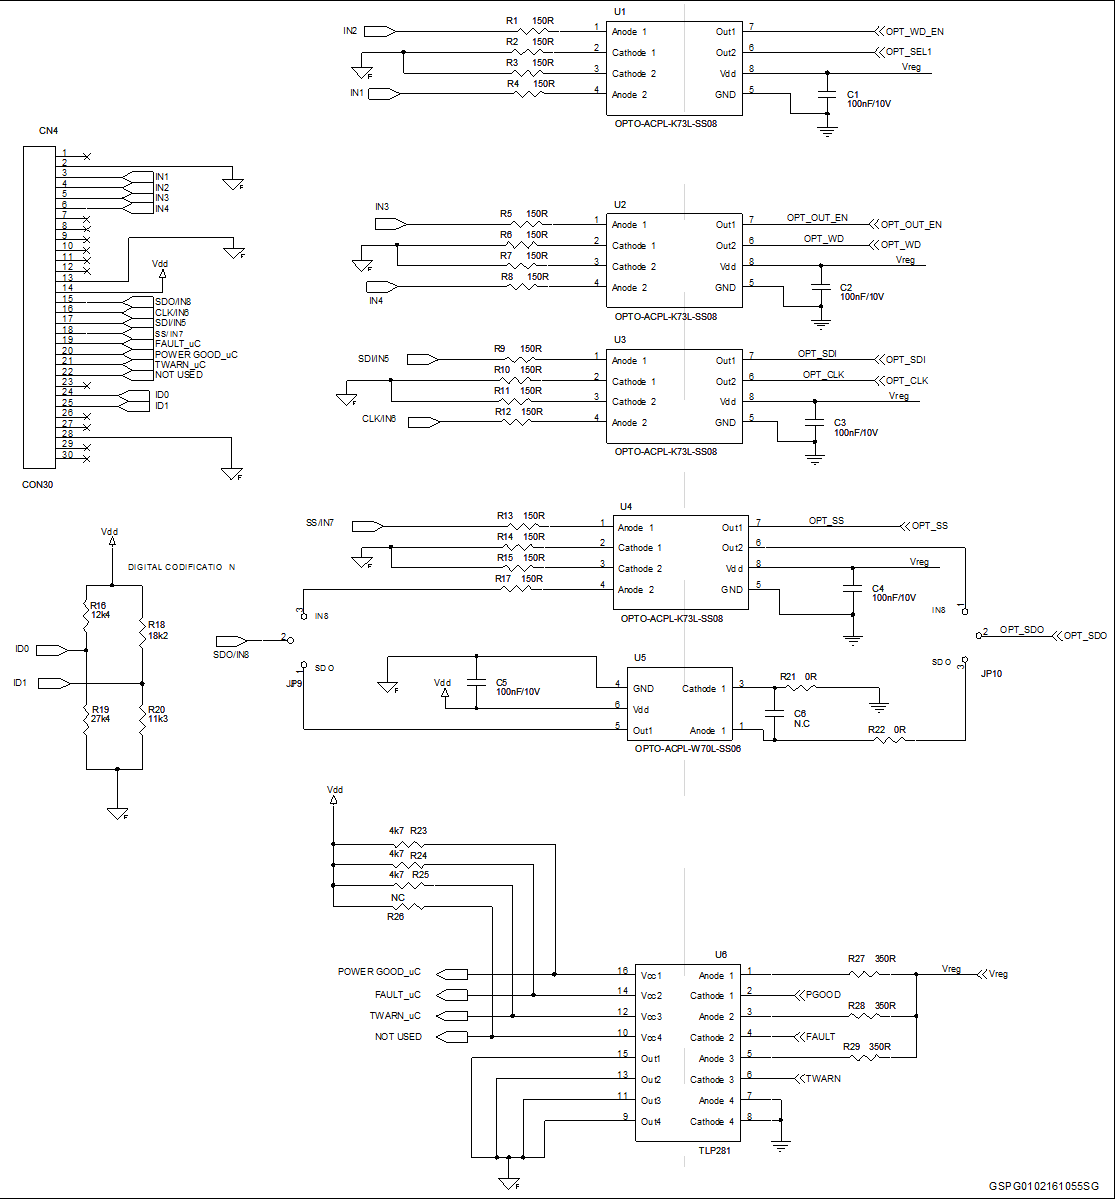
[picture p80: figure]
