lucaskirschner/trabajo-final-cese/hardware/doc/Manuales y hojas de datos/STEVAL-IFP007V1 Schematics.pdf

STEVAL-IFP007V1 | Circuit schematic

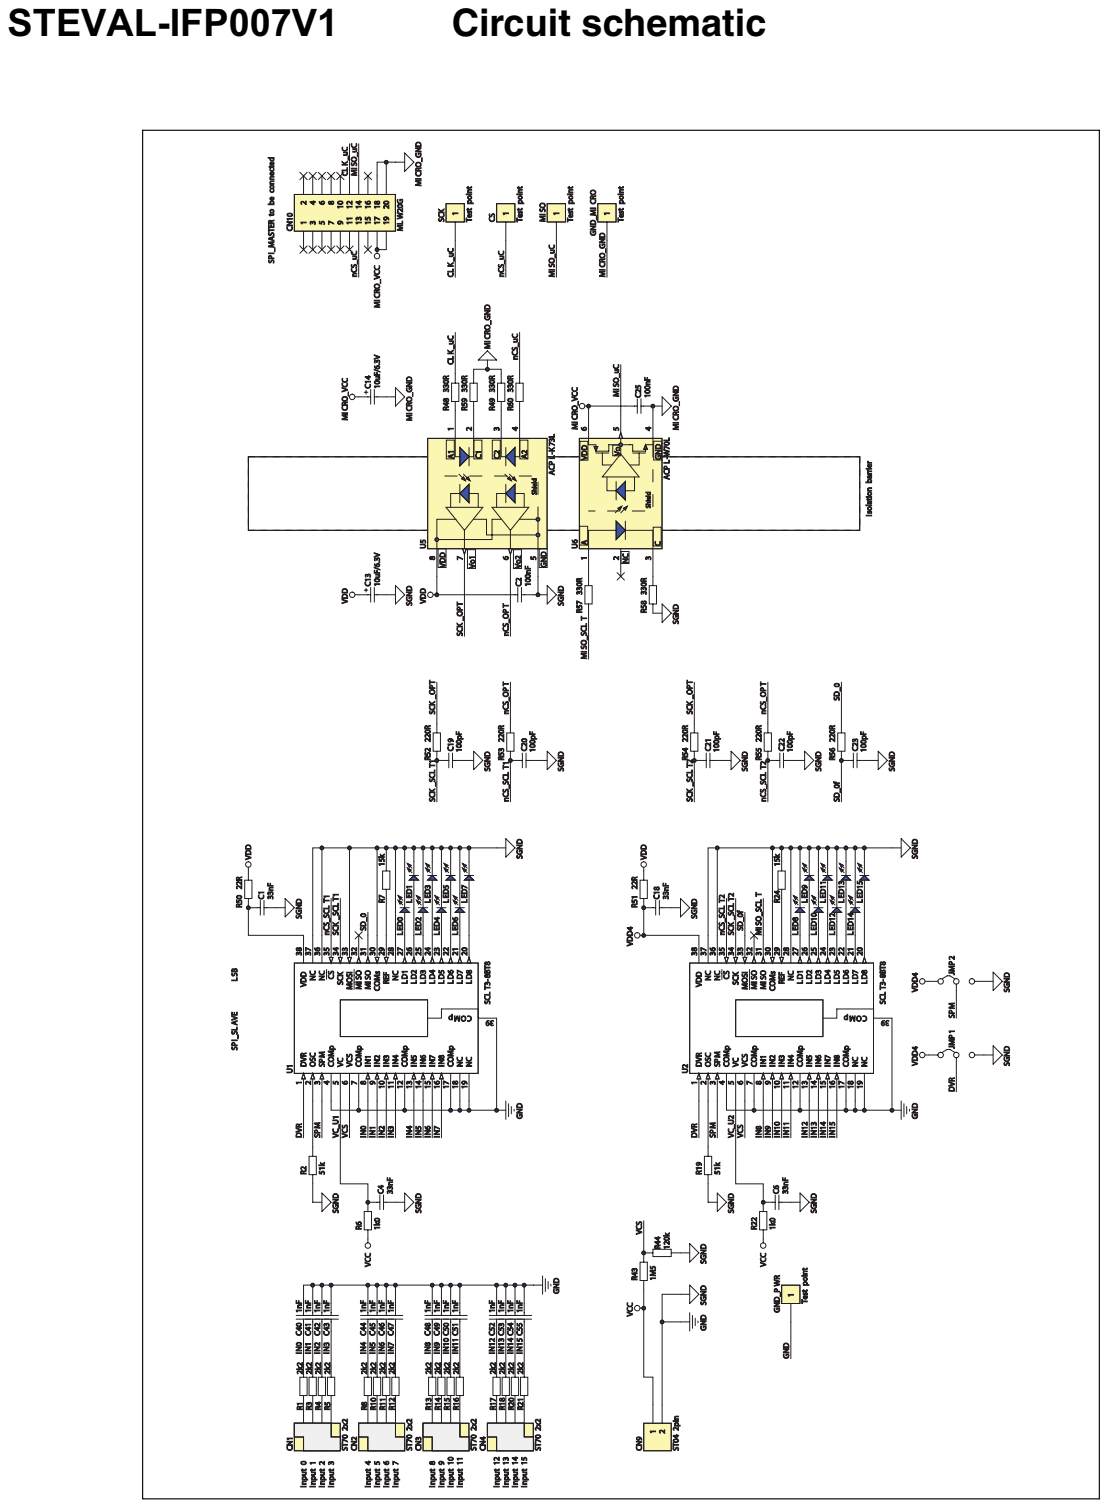
[picture p93: page 1]

REF 29 COMs 30 MI SO 31 MI SO 32 MOSI 33 SCK 34

DVR SPM JMP 1 JMP 2
