lucaskirschner/trabajo-final-cese/hardware/dev/Rev/MEC-V1.0-PCB RevD.pdf

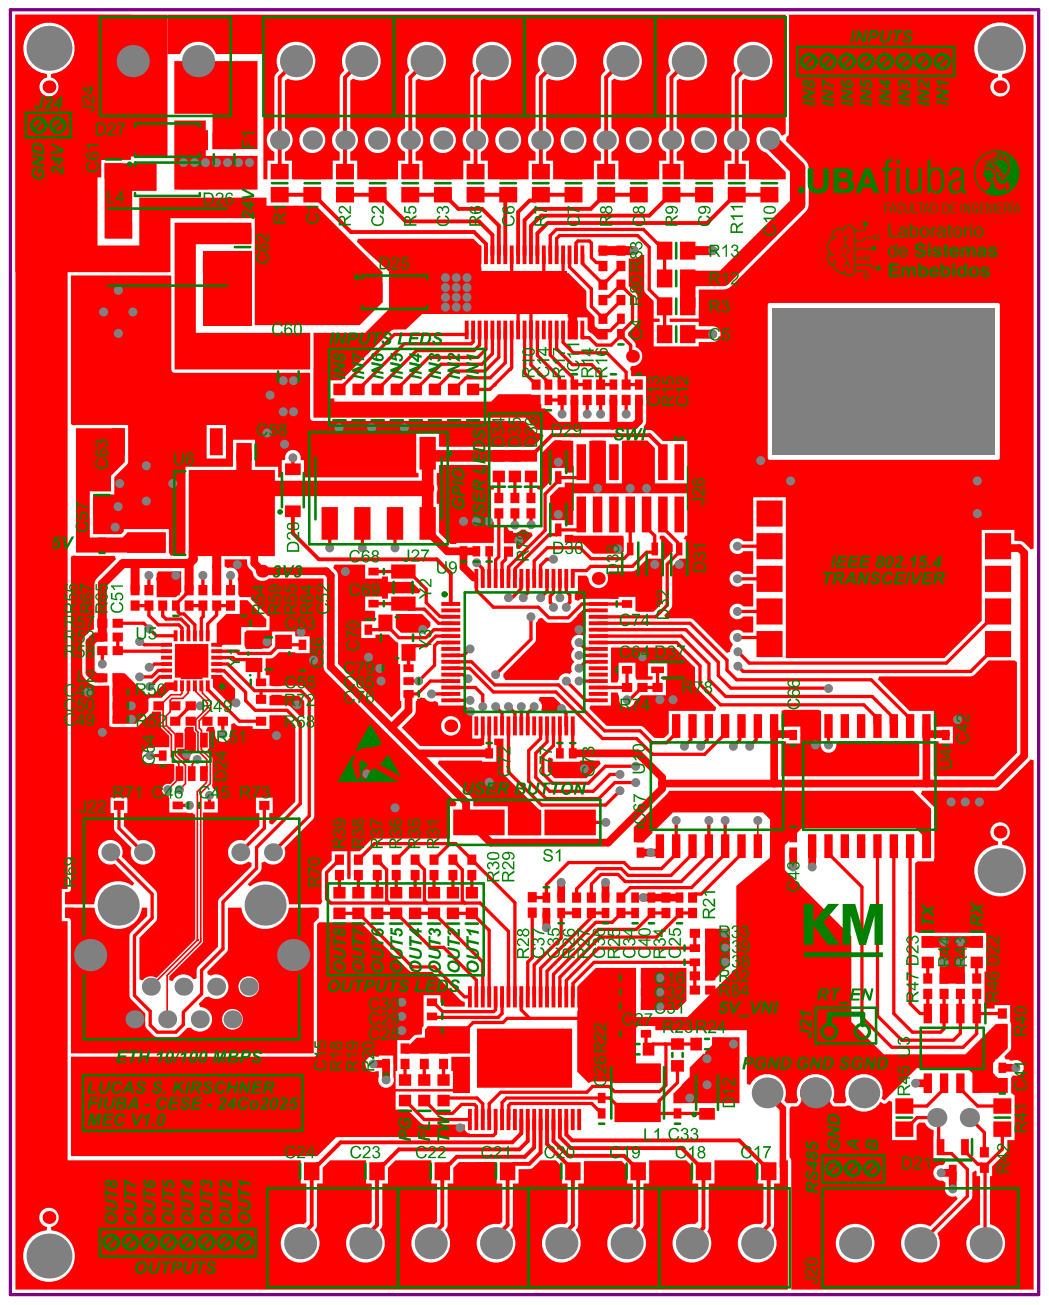
[picture p95: page 1]

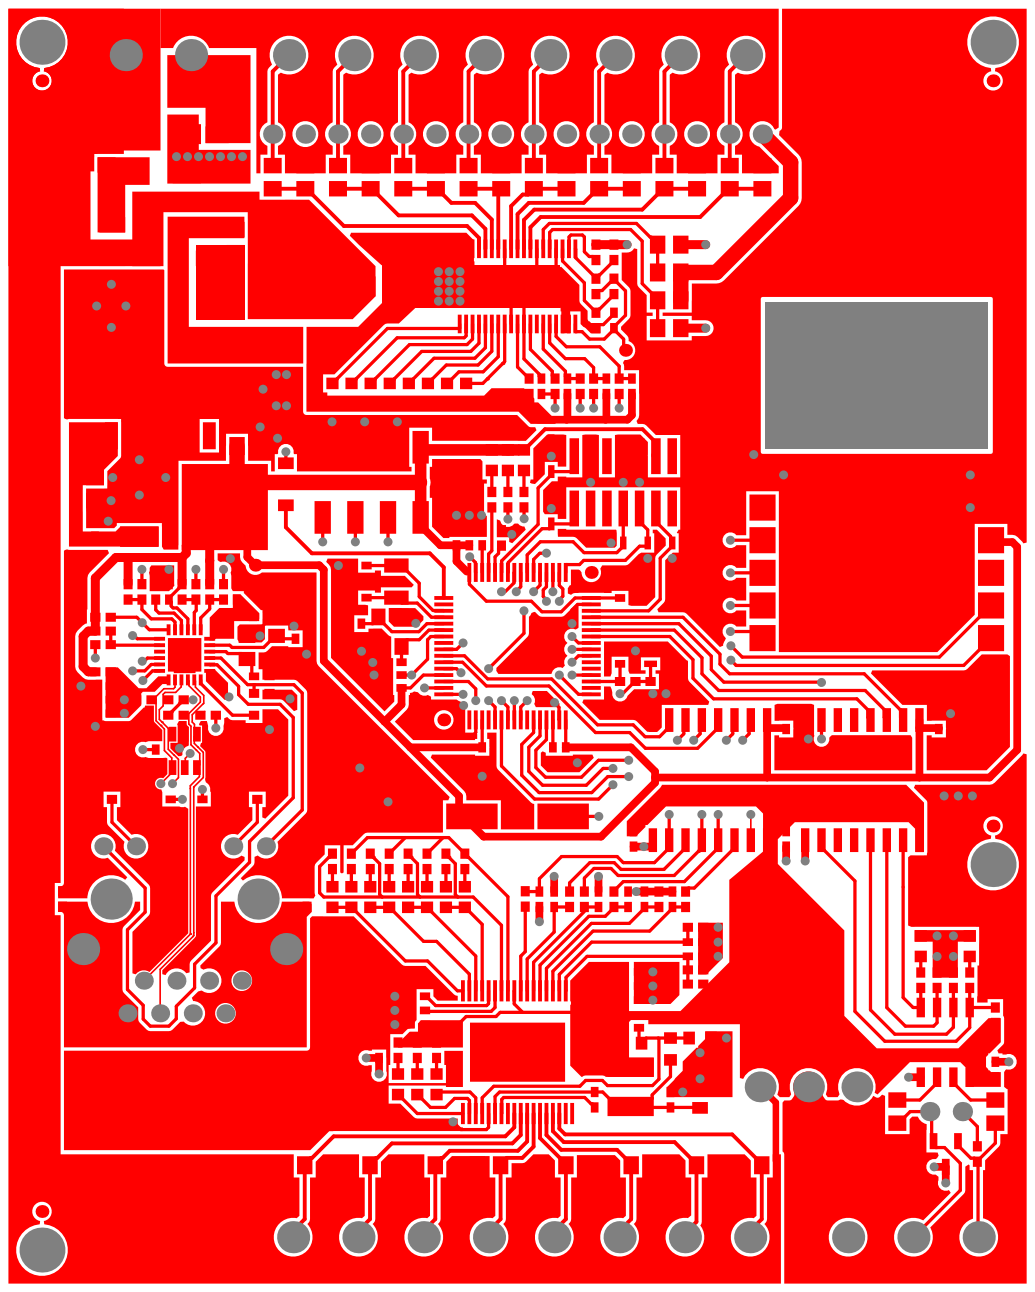
[picture p96: page 2]

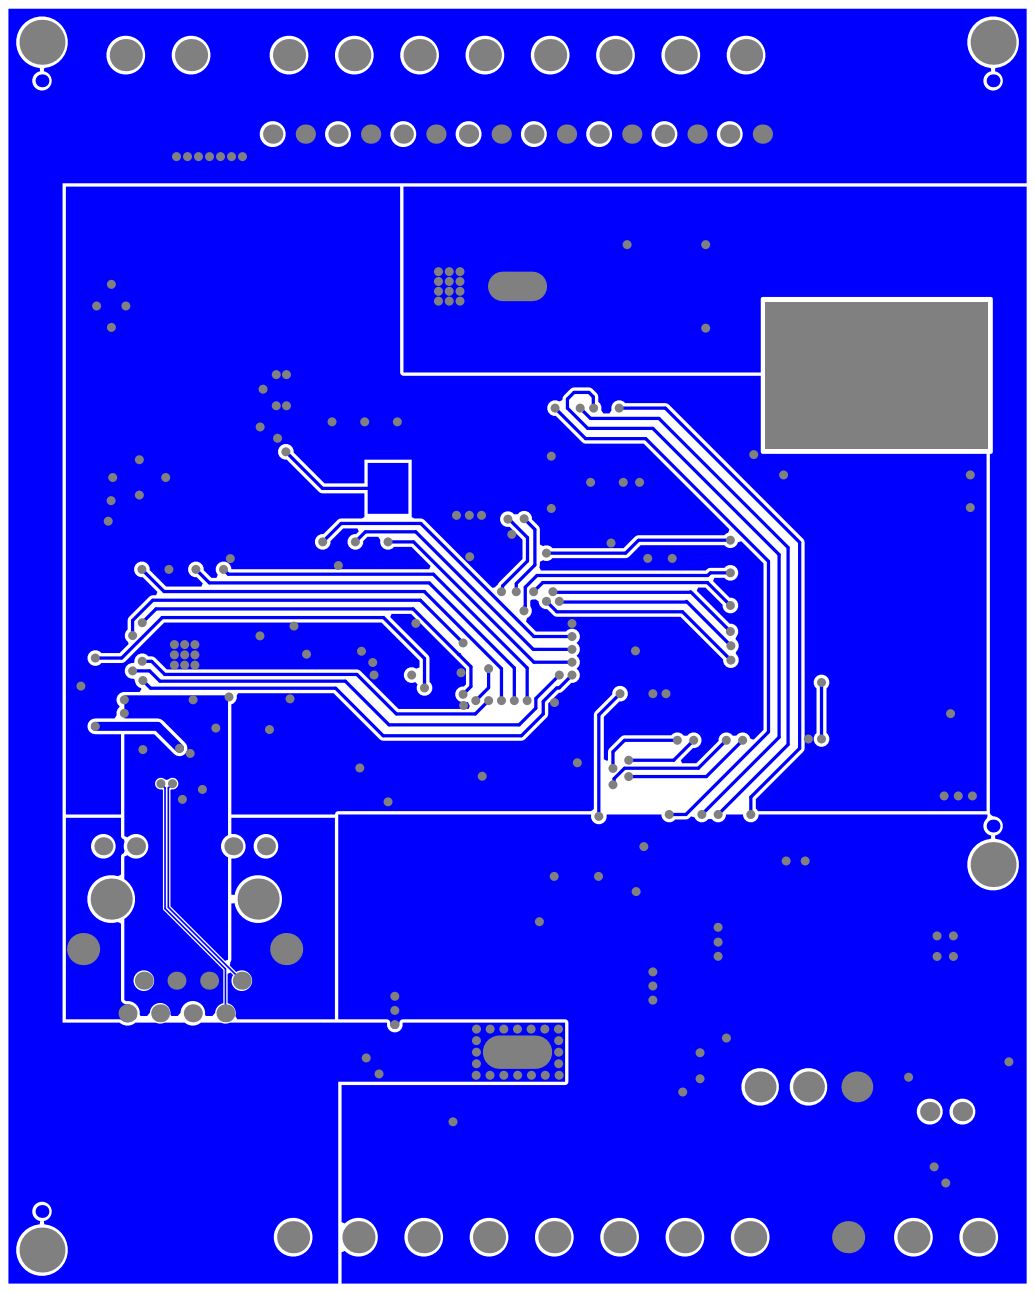
[picture p97: page 3]
