lucaskirschner/trabajo-final-cese/hardware/dev/Rev/MEC-V1.0-PCB RevA.pdf

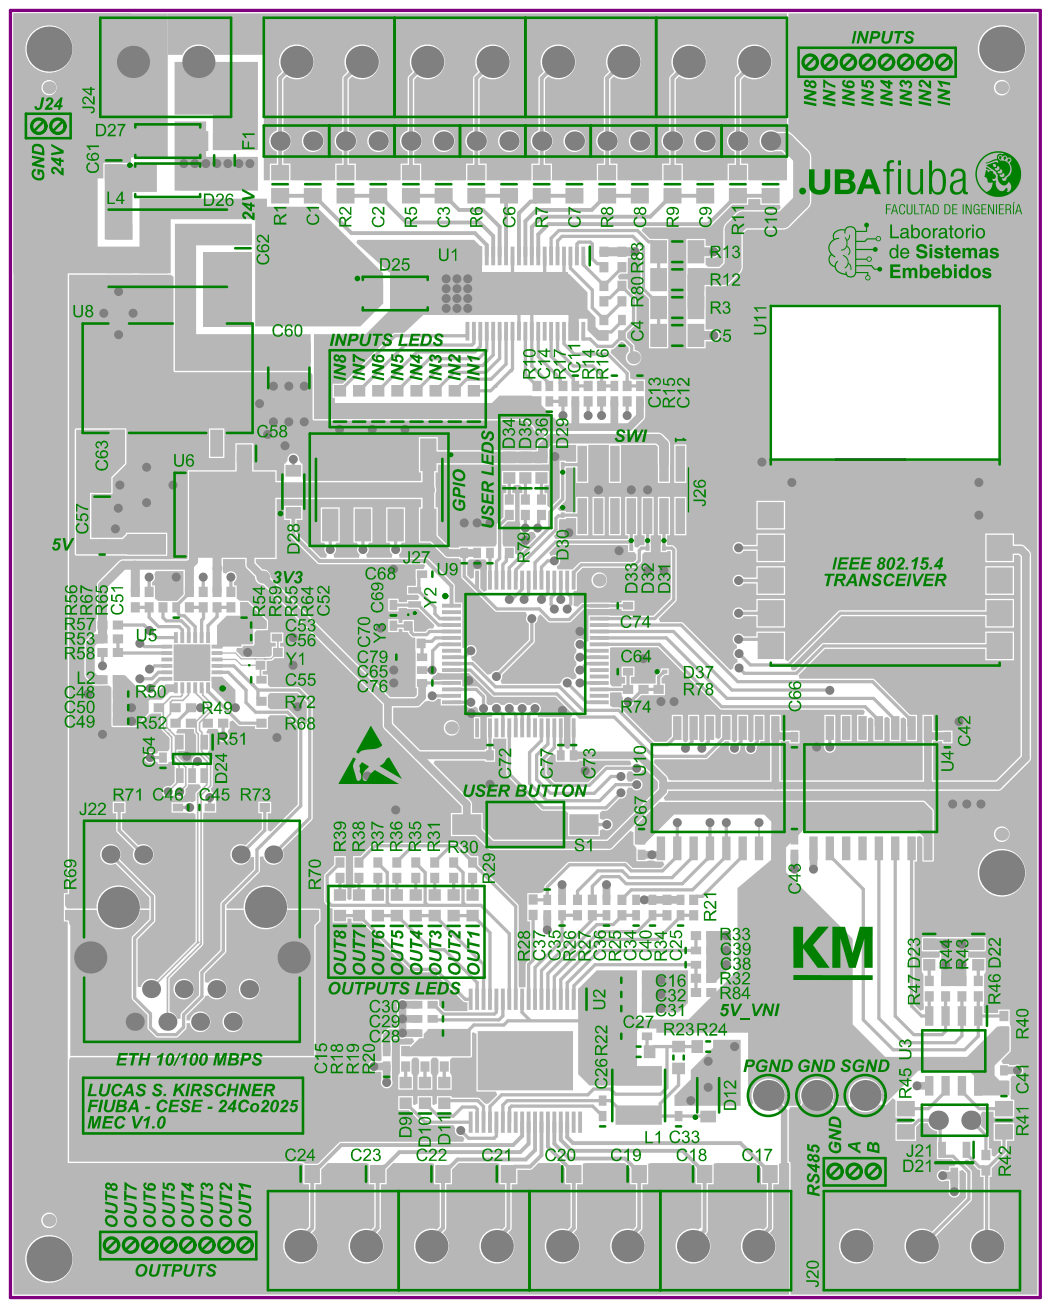
[picture p98: page 1]

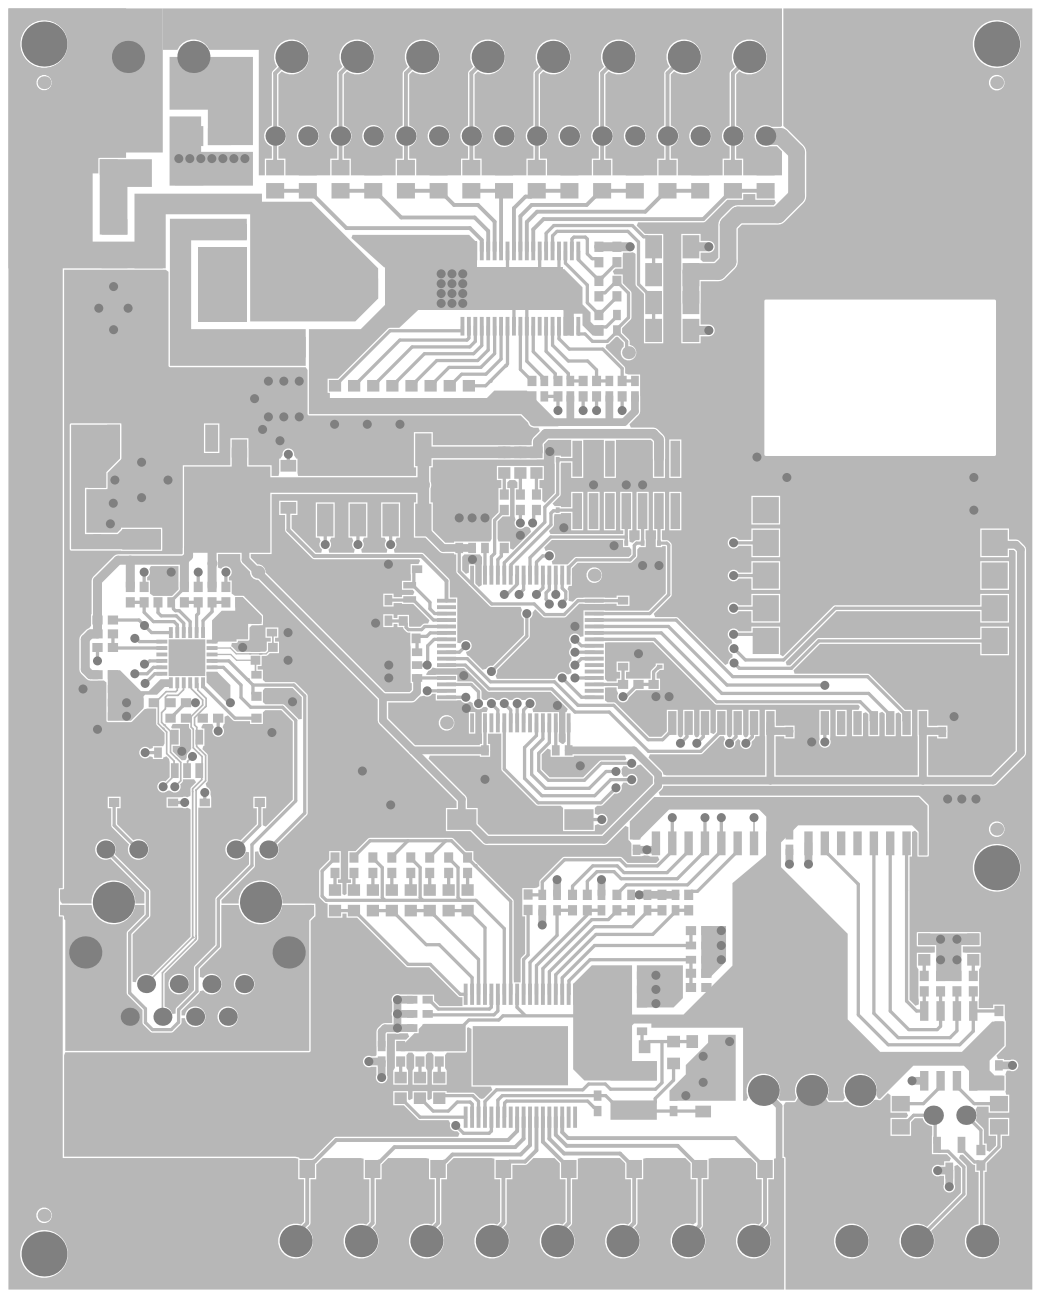
[picture p99: page 2]

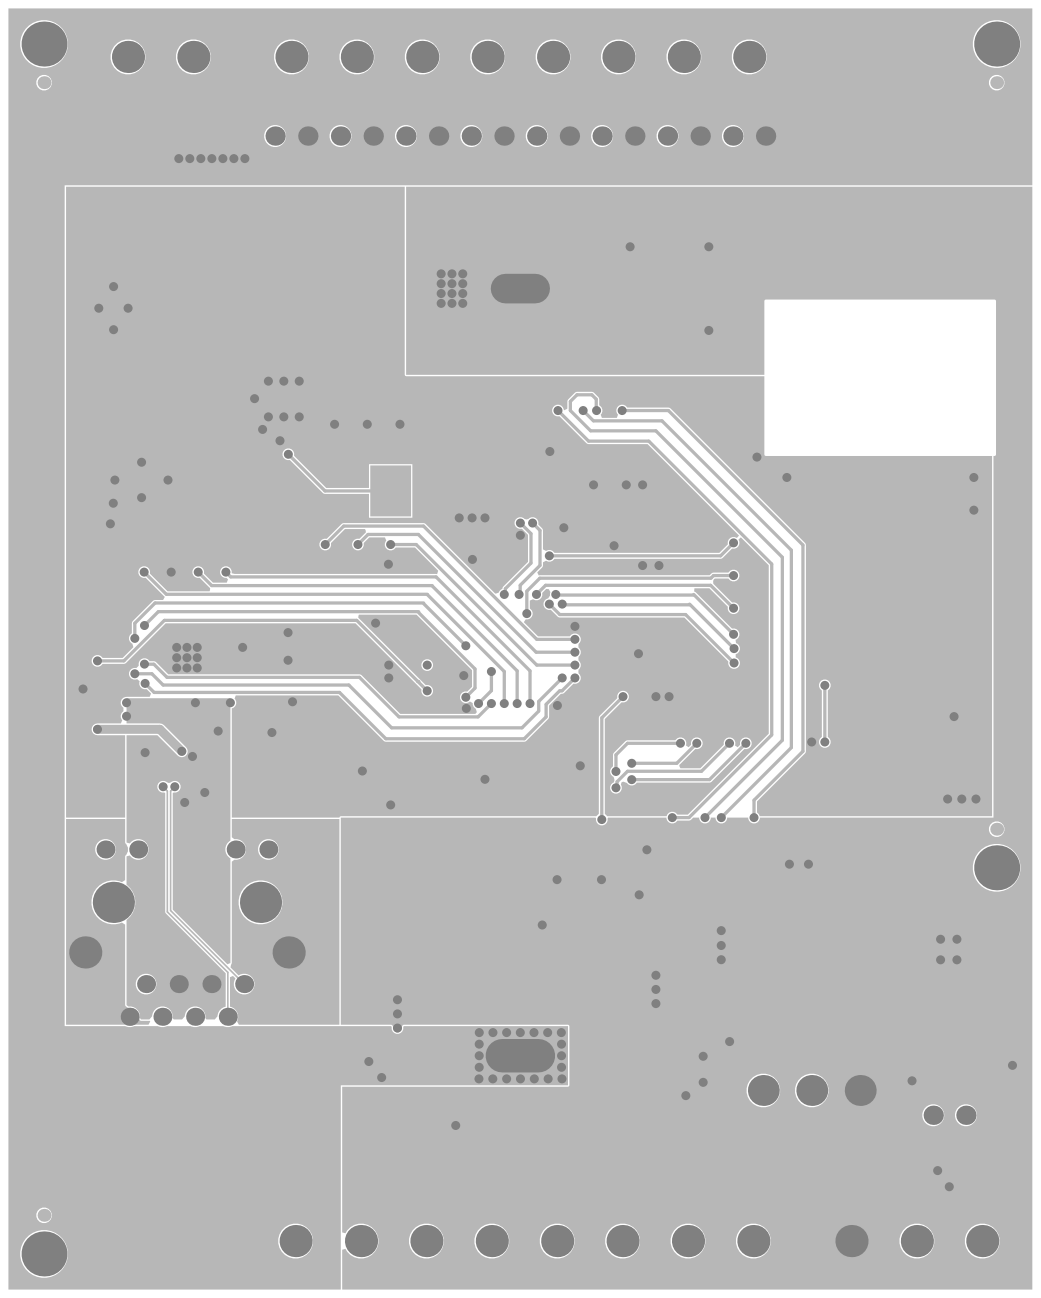
[picture p100: page 3]
