lucaskirschner/trabajo-final-cese/hardware/dev/Rev/MEC-V1.0-PCB RevB.pdf

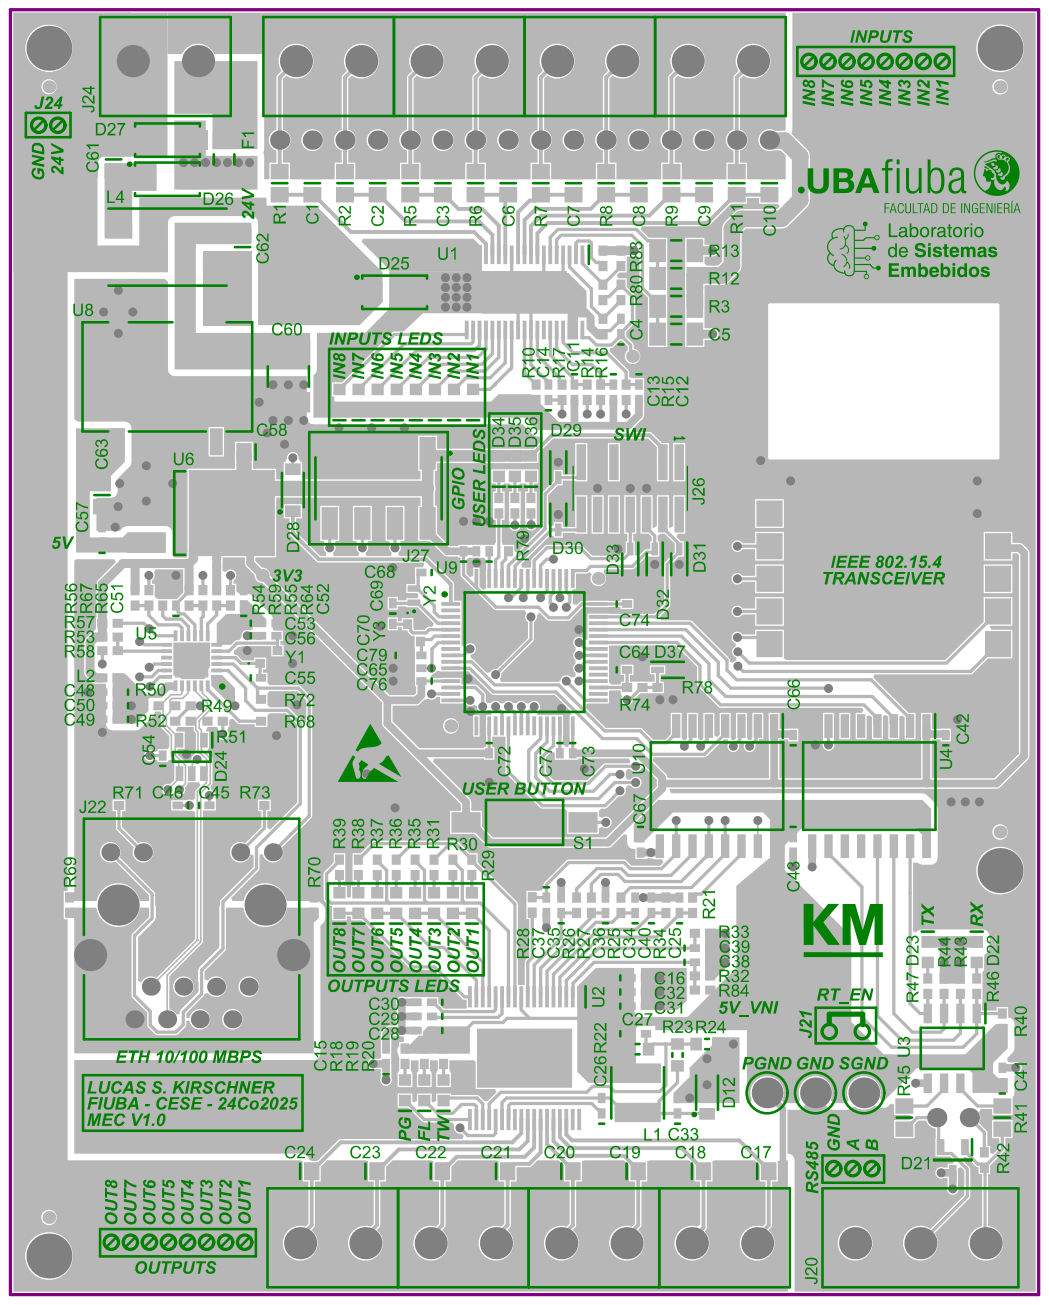
[picture p101: page 1]

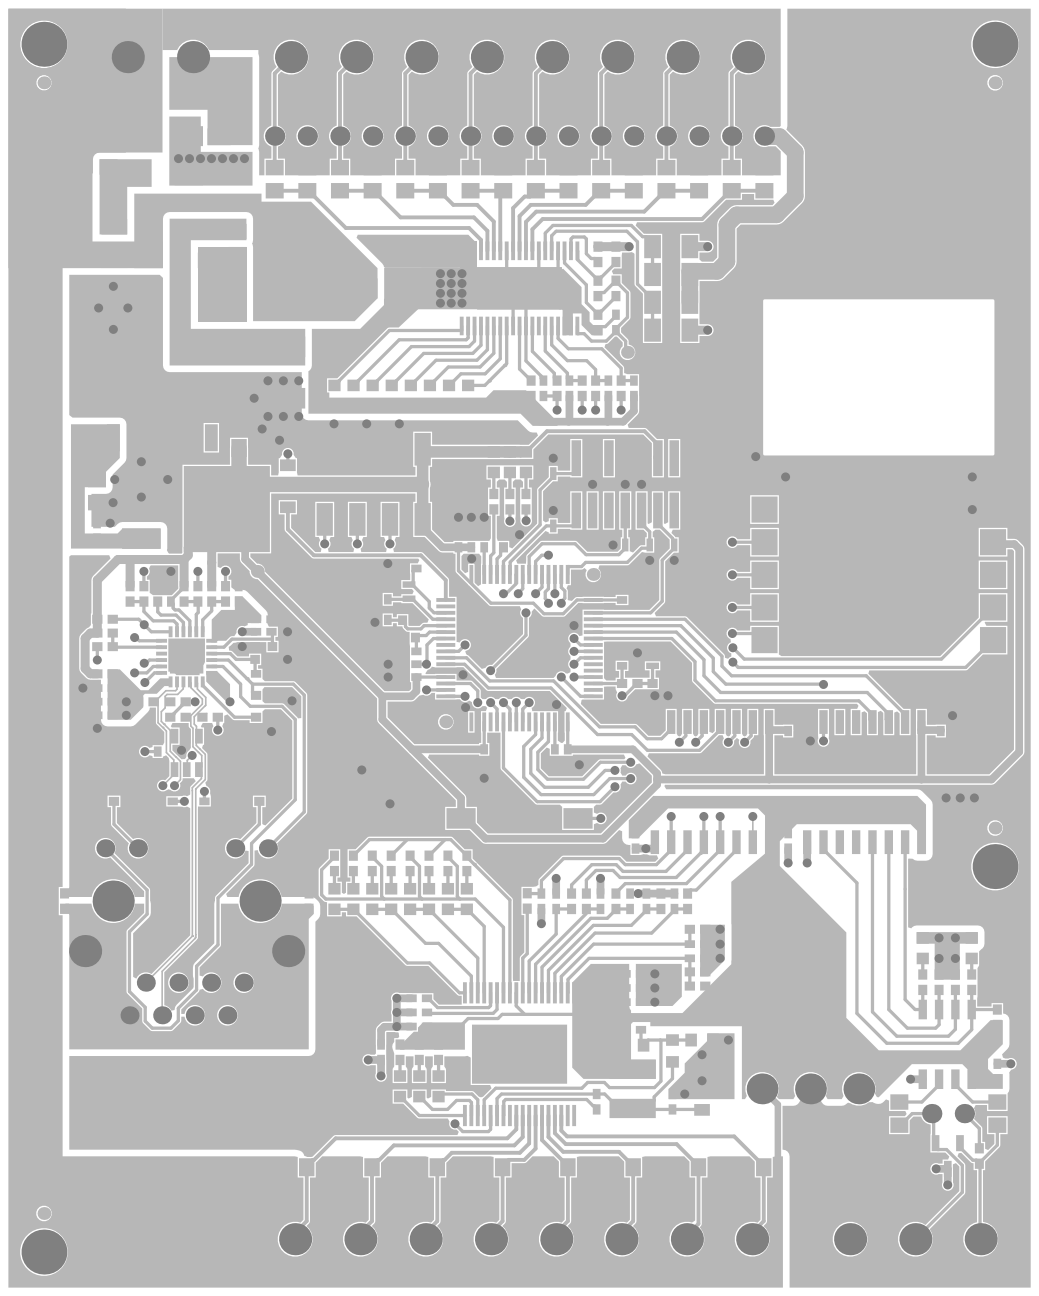
[picture p102: page 2]

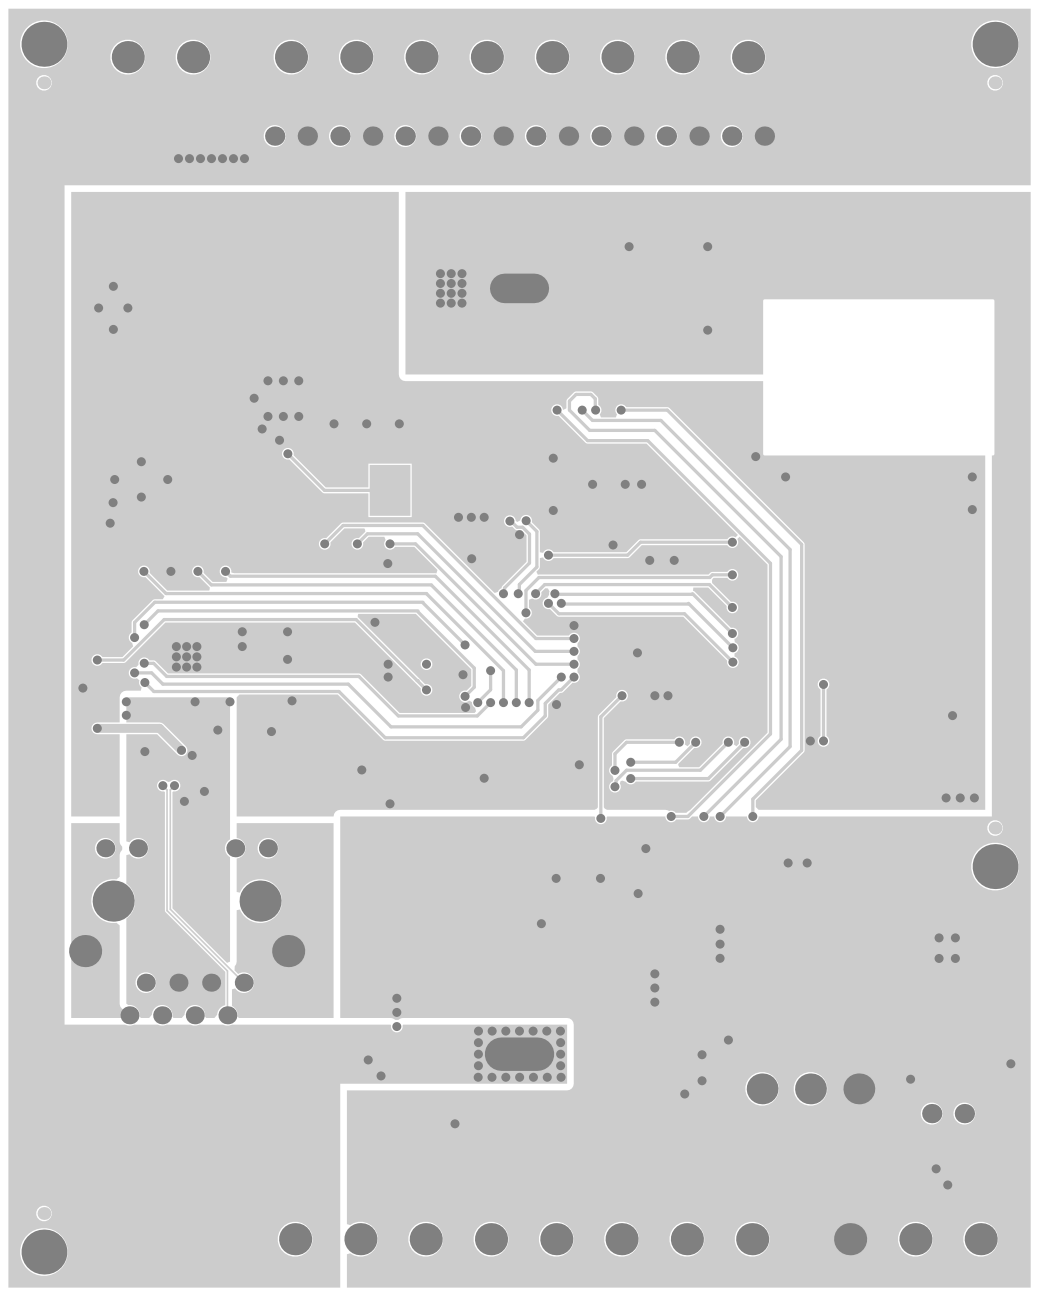
[picture p103: page 3]
