lucaskirschner/trabajo-final-cese/memoria/Figures/arquitectura_slave.pdf

# ESTACIÓN REMOTA

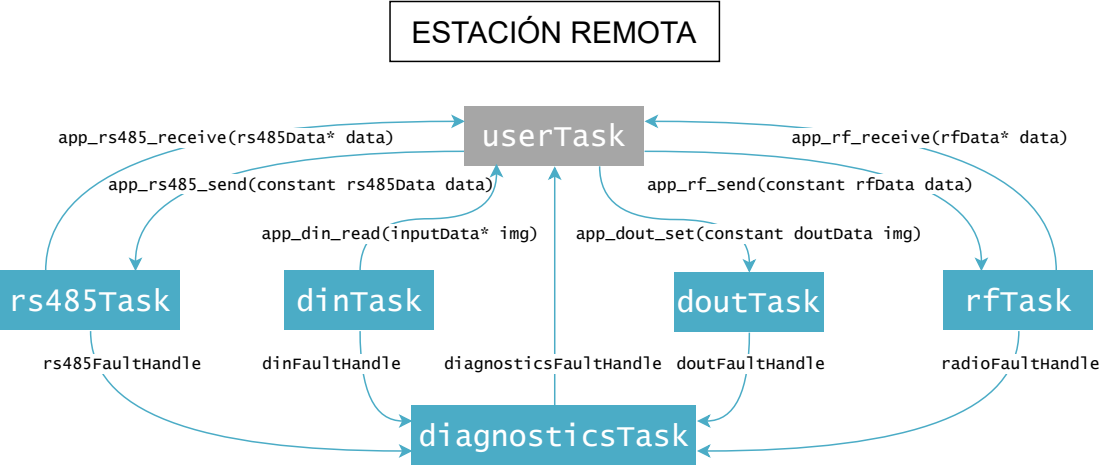
[picture p104: page 1]
app_rs485_send(constant rs485Data data); app_rf_send(constant rfData data); userTask; app_rf_receive(rfData* data); radioFaultHandle; rfTask; diagnosticsFaultHandle; diagnosticsTask; app_rs485_receive(rs485Data* data); rs485FaultHandle; rs485Task; dinFaultHandle; dinTask; doutFaultHandle; doutTask; app_din_read(inputData* img)

app_dout_set(constant doutData img)
