lucaskirschner/trabajo-final-cese/memoria/Figures/arquitectura_general.pdf

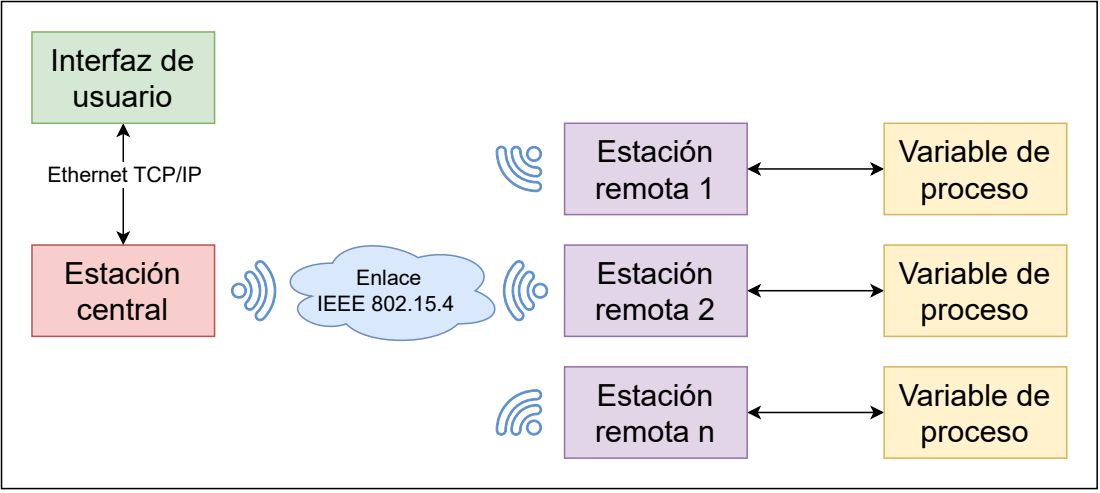
[picture p105: page 1]
Estación central; Estación remota 1; Estación remota 2; Estación remota n; Interfaz de usuario; Enlace IEEE 802.15.4; Variable de proceso

Ethernet TCP/IP
