lucaskirschner/trabajo-final-cese/firmware/MEC-SCMCII-COORDINATOR/System/BSP/IO/io_port.c

/******************************************************************************
 * Copyright (c) 2026, Lucas Kirschner <kirschnerlucas1@gmail.com>
 *
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
 * SPDX-License-Identifier: MIT
 ******************************************************************************/

/**
 * @file    io_port.c
 * @author  Lucas Kirschner <kirschnerlucas1@gmail.com>
 * @date    2026-04-20
 * @brief   Shared SPI1 port implementation for industrial input/output modules.
 *
 * @details
 * This module serializes access to the shared SPI1 bus using a CMSIS-RTOS2
 * mutex.
 *
 * Uses:
 *  - SPI1 via HAL SPI services.
 *  - CS pin for VNI8200XP-32: SPI1_CS_VNI_Pin.
 *  - CS pin for SCLT3-8BT8: SPI1_CS_CLT_Pin.
 *  - main.h is included to reuse CubeMX pin macros.
 *
 * Only one task can perform a SPI transaction at a time. Chip select assertion,
 * SPI transfer and chip select deassertion are protected as a single critical
 * bus transaction.
 *
 * @ingroup io_port
 * @{
 */

/* ============================= Includes ================================== */

#include "io_port.h"
#include "main.h"
#include "stm32h5xx_hal.h"
#include "cmsis_os2.h"

/* ============================ Local Macros =============================== */

/**
 * @brief SPI timeout used by blocking HAL transfers.
 */
#define IO_PORT_SPI_TIMEOUT_MS                  ((uint32_t)100u)

/**
 * @brief Maximum time to wait for exclusive access to the shared SPI bus.
 */
#define IO_PORT_MUTEX_TIMEOUT_MS                ((uint32_t)100u)

/* ======================= External RTOS Objects ============================ */

/**
 * @brief Mutex used to serialize access to the shared SPI1 bus.
 *
 * @details
 * This mutex must be created by CubeMX before any task can access this module.
 */
extern osMutexId_t ioPortSpiMutexHandle;

/* ======================= Local Static Variables ========================== */

extern SPI_HandleTypeDef hspi2;
static SPI_HandleTypeDef * const hspi = &hspi2;

/* ========================== Private Prototypes =========================== */

static bool io_port_is_valid_device(io_port_device_t device);
static void io_port_cs_assert(io_port_device_t device);
static void io_port_cs_deassert(io_port_device_t device);
static io_port_status_t io_port_mutex_acquire(void);
static void io_port_mutex_release(void);
static io_port_status_t io_port_from_hal_status(HAL_StatusTypeDef status);

/* ===================== Public Function Definitions ======================= */

io_port_status_t io_port_transmit_receive(io_port_device_t device,
                                          const uint8_t * const tx_buffer,
                                          uint8_t * const rx_buffer,
                                          size_t length)
{
    HAL_StatusTypeDef hal_status;
    io_port_status_t status;

    if ((tx_buffer == NULL) || (rx_buffer == NULL))
    {
        return IO_PORT_E_NULL;
    }

    if ((io_port_is_valid_device(device) == false) || (length == 0u))
    {
        return IO_PORT_E_PARAM;
    }

    status = io_port_mutex_acquire();

    if (status != IO_PORT_OK)
    {
        return status;
    }

    io_port_cs_assert(device);

    hal_status = HAL_SPI_TransmitReceive(hspi,
                                         (uint8_t *)tx_buffer,
                                         rx_buffer,
                                         (uint16_t)length,
                                         IO_PORT_SPI_TIMEOUT_MS);

    io_port_cs_deassert(device);
    io_port_mutex_release();

    return io_port_from_hal_status(hal_status);
}

io_port_status_t io_port_transmit(io_port_device_t device,
                                  const uint8_t * const tx_buffer,
                                  size_t length)
{
    HAL_StatusTypeDef hal_status;
    io_port_status_t status;

    if (tx_buffer == NULL)
    {
        return IO_PORT_E_NULL;
    }

    if ((io_port_is_valid_device(device) == false) || (length == 0u))
    {
        return IO_PORT_E_PARAM;
    }

    status = io_port_mutex_acquire();

    if (status != IO_PORT_OK)
    {
        return status;
    }

    io_port_cs_assert(device);

    hal_status = HAL_SPI_Transmit(hspi,
                                  (uint8_t *)tx_buffer,
                                  (uint16_t)length,
                                  IO_PORT_SPI_TIMEOUT_MS);

    io_port_cs_deassert(device);
    io_port_mutex_release();

    return io_port_from_hal_status(hal_status);
}

io_port_status_t io_port_receive(io_port_device_t device,
                                 uint8_t * const rx_buffer,
                                 size_t length)
{
    HAL_StatusTypeDef hal_status;
    io_port_status_t status;

    if (rx_buffer == NULL)
    {
        return IO_PORT_E_NULL;
    }

    if ((io_port_is_valid_device(device) == false) || (length == 0u))
    {
        return IO_PORT_E_PARAM;
    }

    status = io_port_mutex_acquire();

    if (status != IO_PORT_OK)
    {
        return status;
    }

    io_port_cs_assert(device);

    hal_status = HAL_SPI_Receive(hspi,
                                 rx_buffer,
                                 (uint16_t)length,
                                 IO_PORT_SPI_TIMEOUT_MS);

    io_port_cs_deassert(device);
    io_port_mutex_release();

    return io_port_from_hal_status(hal_status);
}

/* ===================== Private Function Definitions ====================== */

/**
 * @brief Check whether the specified device identifier is valid.
 *
 * @param device Device identifier to validate.
 *
 * @return
 * - true: Valid device identifier.
 * - false: Invalid device identifier.
 */
static bool io_port_is_valid_device(io_port_device_t device)
{
    bool is_valid = false;

    switch (device)
    {
        case IO_PORT_DEVICE_SCLT3:
        case IO_PORT_DEVICE_VNI8200XP32:
            is_valid = true;
            break;

        case IO_PORT_DEVICE_NONE:
        default:
            is_valid = false;
            break;
    }

    return is_valid;
}

/**
 * @brief Assert the selected device chip select signal.
 *
 * @param device Target device.
 *
 * @details
 * Chip select signals are active low.
 */
static void io_port_cs_assert(io_port_device_t device)
{
    switch (device)
    {
        case IO_PORT_DEVICE_SCLT3:
            HAL_GPIO_WritePin(SPI2_CS_CLT_GPIO_Port,
                              SPI2_CS_CLT_Pin,
                              GPIO_PIN_RESET);
            break;

        case IO_PORT_DEVICE_VNI8200XP32:
            HAL_GPIO_WritePin(SPI2_CS_VNI_GPIO_Port,
                              SPI2_CS_VNI_Pin,
                              GPIO_PIN_RESET);
            break;

        case IO_PORT_DEVICE_NONE:
        default:
            /* No action. */
            break;
    }
}

/**
 * @brief Deassert the selected device chip select signal.
 *
 * @param device Target device.
 *
 * @details
 * Chip select signals are active low.
 */
static void io_port_cs_deassert(io_port_device_t device)
{
    switch (device)
    {
        case IO_PORT_DEVICE_SCLT3:
            HAL_GPIO_WritePin(SPI2_CS_CLT_GPIO_Port,
                              SPI2_CS_CLT_Pin,
                              GPIO_PIN_SET);
            break;

        case IO_PORT_DEVICE_VNI8200XP32:
            HAL_GPIO_WritePin(SPI2_CS_VNI_GPIO_Port,
                              SPI2_CS_VNI_Pin,
                              GPIO_PIN_SET);
            break;

        case IO_PORT_DEVICE_NONE:
        default:
            /* No action. */
            break;
    }
}

/**
 * @brief Acquire exclusive access to the shared SPI bus.
 *
 * @return
 * - IO_PORT_OK: Mutex acquired successfully.
 * - IO_PORT_E_BUSY: Mutex could not be acquired before timeout.
 * - IO_PORT_E_HW: Mutex object is invalid or another RTOS error occurred.
 */
static io_port_status_t io_port_mutex_acquire(void)
{
    osStatus_t mutex_status;
    io_port_status_t status;

    mutex_status = osMutexAcquire(ioPortSpiMutexHandle,
                                  IO_PORT_MUTEX_TIMEOUT_MS);

    switch (mutex_status)
    {
        case osOK:
            status = IO_PORT_OK;
            break;

        case osErrorTimeout:
        case osErrorResource:
            status = IO_PORT_E_BUSY;
            break;

        default:
            status = IO_PORT_E_HW;
            break;
    }

    return status;
}

/**
 * @brief Release exclusive access to the shared SPI bus.
 */
static void io_port_mutex_release(void)
{
    (void)osMutexRelease(ioPortSpiMutexHandle);
}

/**
 * @brief Convert a HAL SPI status code to an I/O port status code.
 *
 * @param status HAL status returned by a blocking SPI function.
 *
 * @return Equivalent I/O port status code.
 */
static io_port_status_t io_port_from_hal_status(HAL_StatusTypeDef status)
{
    io_port_status_t ret;

    switch (status)
    {
        case HAL_OK:
            ret = IO_PORT_OK;
            break;

        case HAL_TIMEOUT:
            ret = IO_PORT_E_TIMEOUT;
            break;

        case HAL_BUSY:
            ret = IO_PORT_E_BUSY;
            break;

        case HAL_ERROR:
        default:
            ret = IO_PORT_E_HW;
            break;
    }

    return ret;
}

/** @} */
